campy/P3Steel-MGN-V19/P3Steel MGN BMG/Pegatina P3Steel/custom-industrial-write-on-signs-y4323289-65185-m8615-lg.jpg

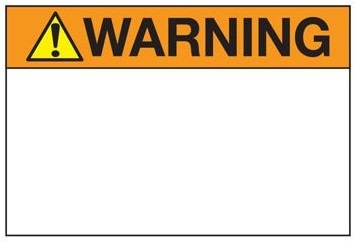
P3Steel MGN BMG/Pegatina P3Steel/custom-industrial-write-on-signs-y4323289-65185-m8615-lg.jpg
