campy/P3Steel-MGN-V19/P3Steel MGN BMG/Pegatina P3Steel/J6014.a24cb0112e51902b6b3ed4606a7cd727.png

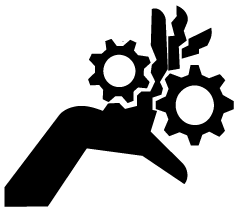
P3Steel MGN BMG/Pegatina P3Steel/J6014.a24cb0112e51902b6b3ed4606a7cd727.png
