campy/P3Steel-MGN-V19/P3Steel MGN BMG/Pegatina P3Steel/J6804.png

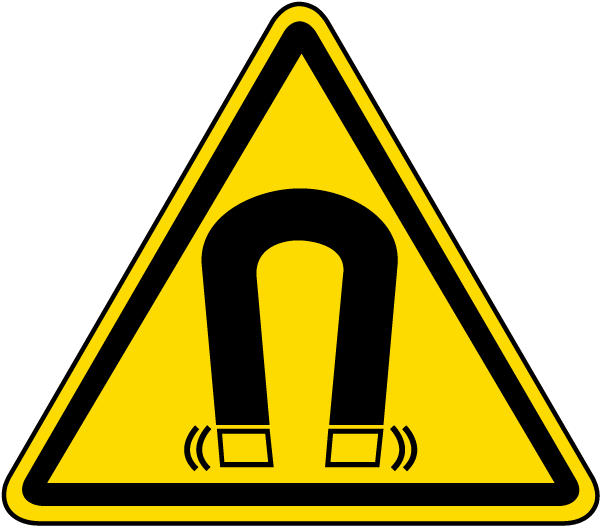
P3Steel MGN BMG/Pegatina P3Steel/J6804.png
