campy/P3Steel-MGN-V19/P3Steel MGN BMG/Pegatina P3Steel/p1725301.jpg

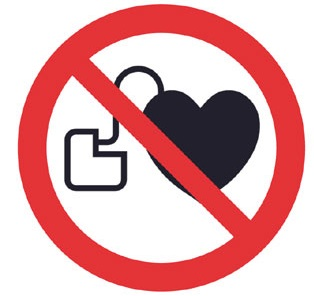
P3Steel MGN BMG/Pegatina P3Steel/p1725301.jpg
