campy/P3Steel-MGN-V19/P3Steel MGN BMG/Pegatina P3Steel/s-l1000.jpg

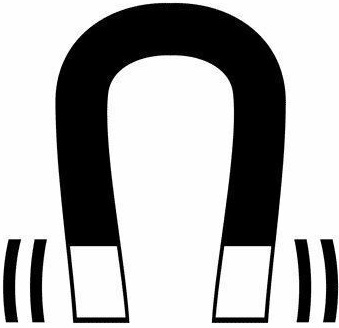
P3Steel MGN BMG/Pegatina P3Steel/s-l1000.jpg
