campy/P3Steel-MGN-V19/P3Steel MGN BMG/Piezas impresas/Soportes electronicas/Placas/MKS Gen L/Gen L.jpg

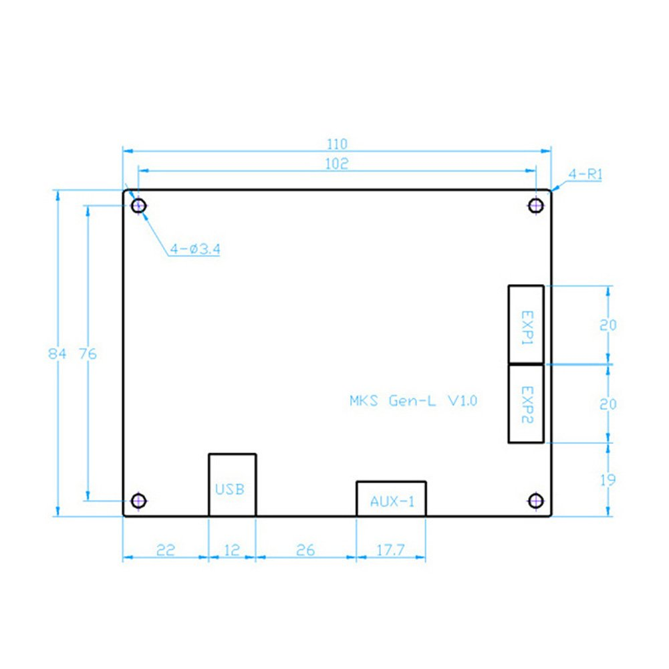
P3Steel MGN BMG/Piezas impresas/Soportes electronicas/Placas/MKS Gen L/Gen L.jpg
