campy/P3Steel-MGN-V19/P3Steel MGN BMG/Source/F-Sensor/Bildschirmfoto 2016-11-22 um 21.45.32.JPG

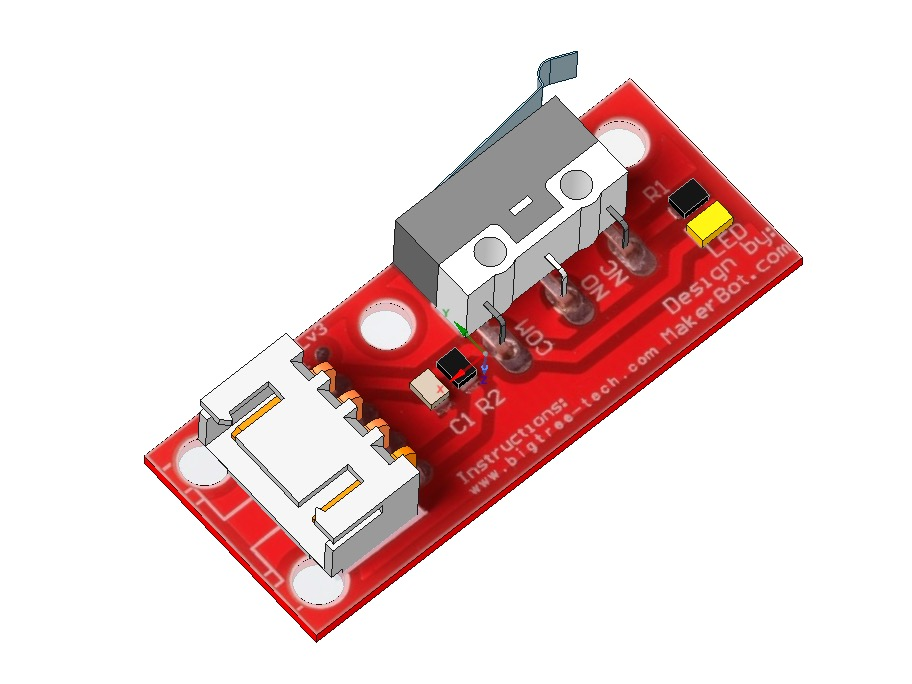
P3Steel MGN BMG/Source/F-Sensor/Bildschirmfoto 2016-11-22 um 21.45.32.JPG
