campy/P3Steel-MGN-V19/P3Steel MGN BMG/Source/Radial Cooling Fan 50mm DC12V/1.JPG

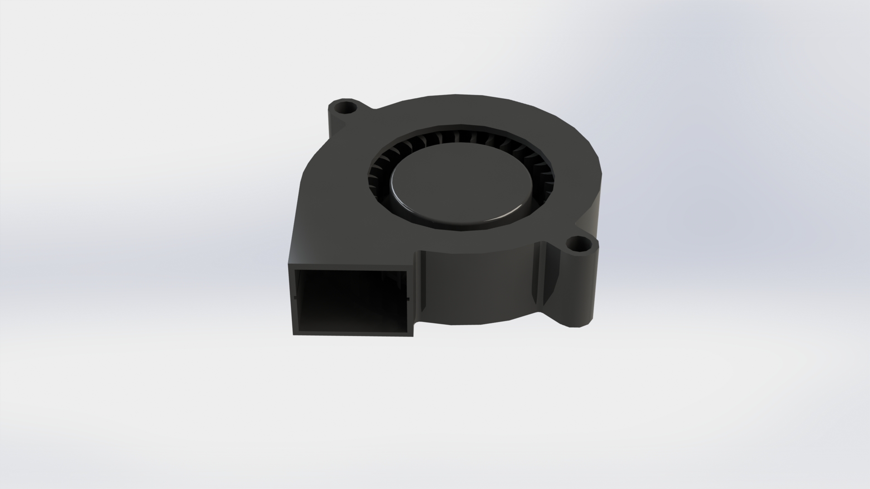
P3Steel MGN BMG/Source/Radial Cooling Fan 50mm DC12V/1.JPG
