campy/P3Steel-MGN-V19/P3Steel MGN BMG/Source/Radial Cooling Fan 50mm DC12V/5015 fan.PNG

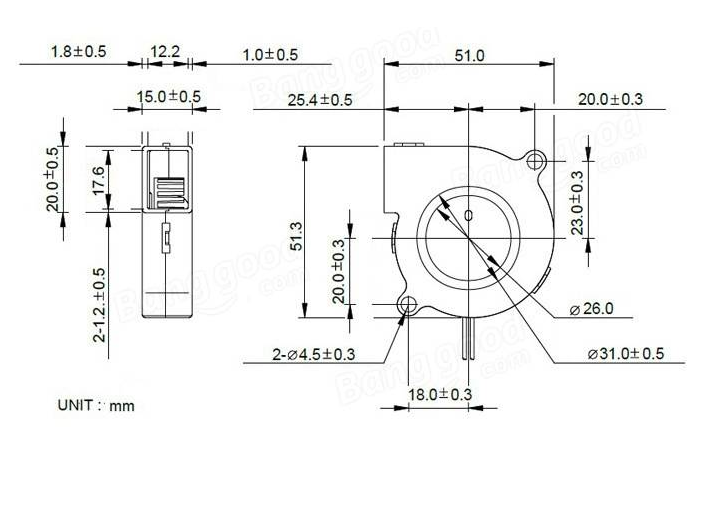
P3Steel MGN BMG/Source/Radial Cooling Fan 50mm DC12V/5015 fan.PNG
