campy/P3Steel-MGN-V19/P3Steel MGN BMG/Source/Radial Cooling Fan 50mm DC12V/Double-50-x-50-x-15mm-12V-DC-50mm-Blow-Radial-Cooling-Fan-for-Electronic-3D.jpg

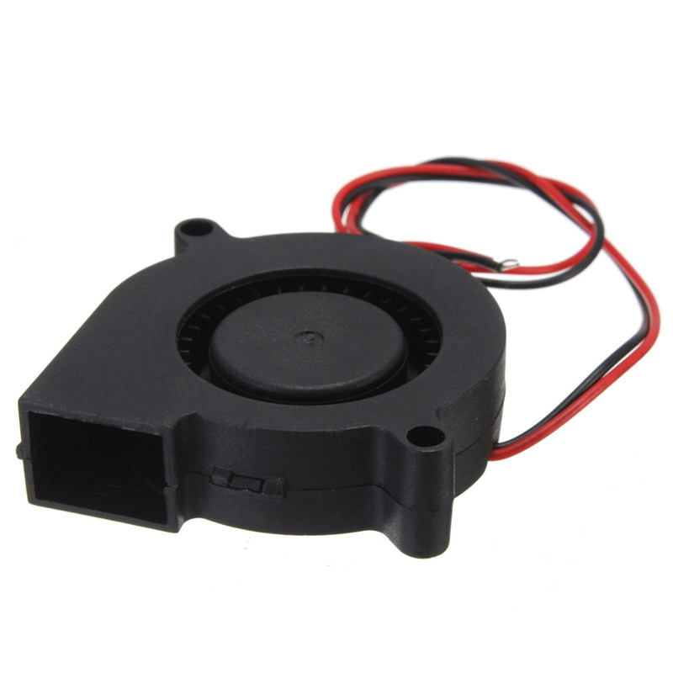
P3Steel MGN BMG/Source/Radial Cooling Fan 50mm DC12V/Double-50-x-50-x-15mm-12V-DC-50mm-Blow-Radial-Cooling-Fan-for-Electronic-3D.jpg
