campy/P3Steel-MGN-V19/P3Steel MGN BMG/Source/Titan Aero/Titan Aero P3steel/Blower titan/images/0aa3240f0cde22aaafeb0d4d7ab34d4f_preview_featured.jpg

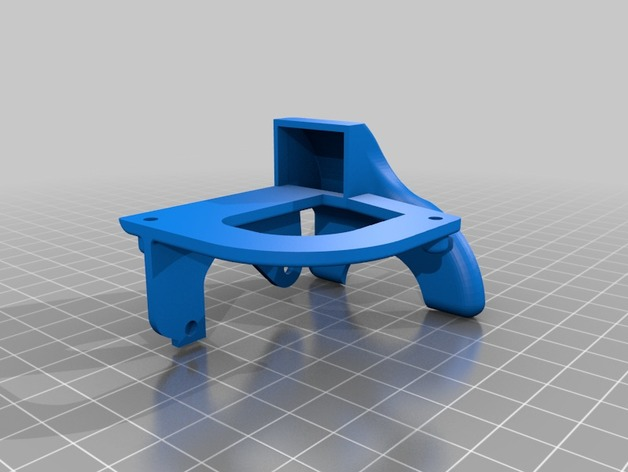
P3Steel MGN BMG/Source/Titan Aero/Titan Aero P3steel/Blower titan/images/0aa3240f0cde22aaafeb0d4d7ab34d4f_preview_featured.jpg
