campy/P3Steel-MGN-V19/P3Steel MGN BMG/Source/Titan Aero/Titan Aero P3steel/Blower titan/images/5dc998a0549c79088eb536fb6c97d659_preview_featured.jpg

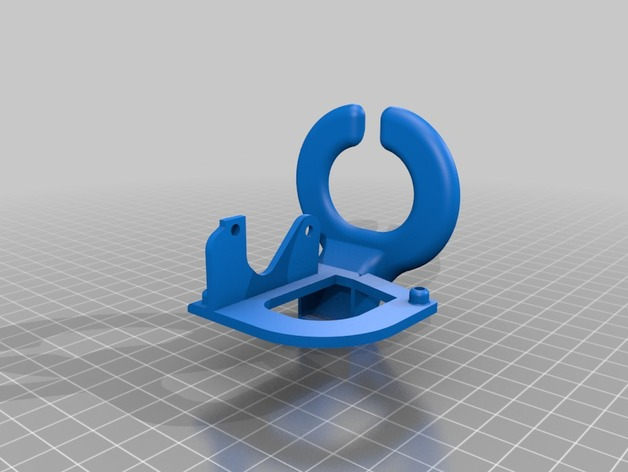
P3Steel MGN BMG/Source/Titan Aero/Titan Aero P3steel/Blower titan/images/5dc998a0549c79088eb536fb6c97d659_preview_featured.jpg
