campy/P3Steel-MGN-V19/P3Steel MGN BMG/Source/Titan Aero/Titan Aero P3steel/Blower titan/images/36a4d80571aeefbeef10a64a5f065d78_preview_featured.jpg

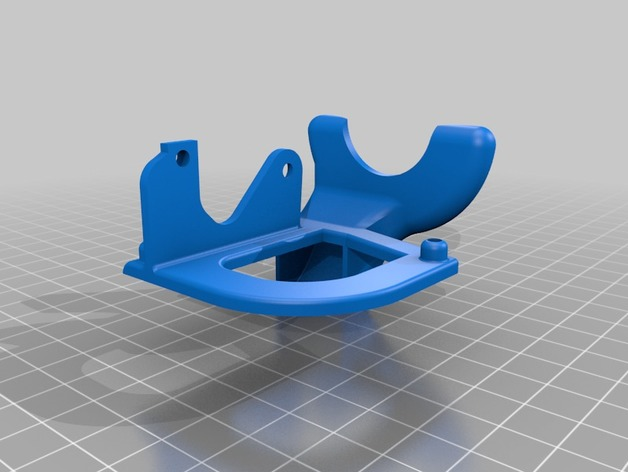
P3Steel MGN BMG/Source/Titan Aero/Titan Aero P3steel/Blower titan/images/36a4d80571aeefbeef10a64a5f065d78_preview_featured.jpg
