campy/P3Steel-MGN-V19/P3Steel MGN BMG/Source/Titan Aero/Titan Aero P3steel/Blower titan/images/036bd3c3c1cbe7b02644d6485af83f34_preview_featured.jpg

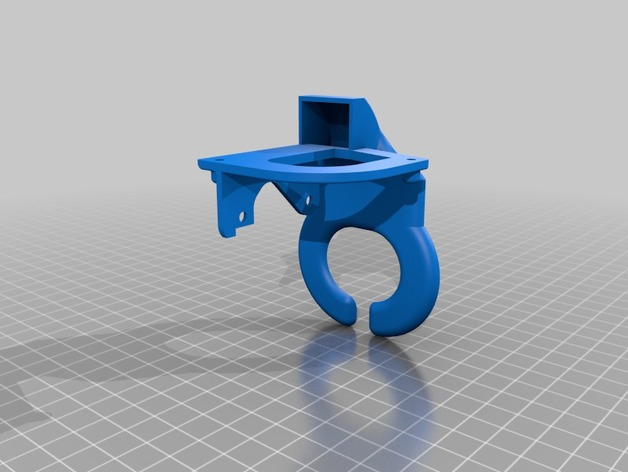
P3Steel MGN BMG/Source/Titan Aero/Titan Aero P3steel/Blower titan/images/036bd3c3c1cbe7b02644d6485af83f34_preview_featured.jpg
