campy/P3Steel-MGN-V19/P3Steel MGN BMG/Source/Titan Aero/Titan Aero P3steel/Blower titan/images/709aa3053908a7bdff81a3a324b6f3b1_preview_featured.jpg

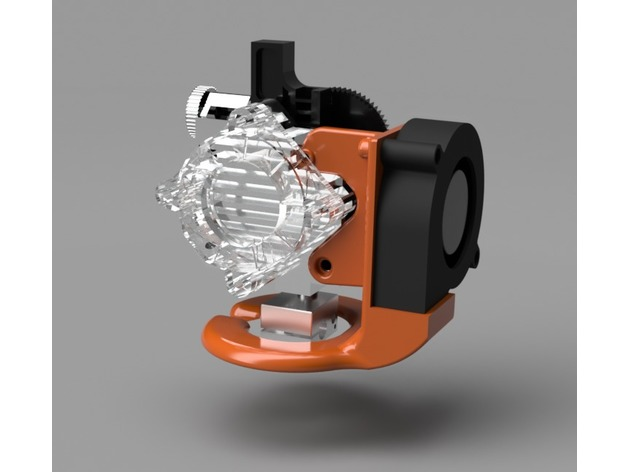
P3Steel MGN BMG/Source/Titan Aero/Titan Aero P3steel/Blower titan/images/709aa3053908a7bdff81a3a324b6f3b1_preview_featured.jpg
