campy/P3Steel-MGN-V19/P3Steel MGN BMG/Source/Titan Aero/Titan Aero P3steel/Blower titan/images/1118b5d8f00bb2cfa117ddb364b9ccff_preview_featured.jpg

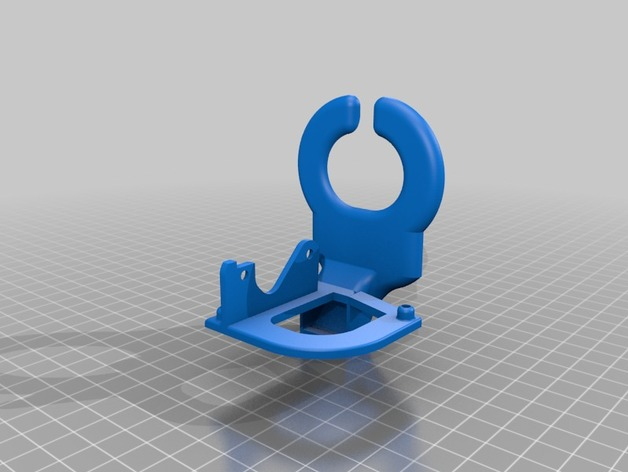
P3Steel MGN BMG/Source/Titan Aero/Titan Aero P3steel/Blower titan/images/1118b5d8f00bb2cfa117ddb364b9ccff_preview_featured.jpg
