campy/P3Steel-MGN-V19/P3Steel MGN BMG/Source/Titan Aero/Titan Aero P3steel/Blower titan/images/51332b5f8a75edf978d1d0842197646b_preview_featured.jpg

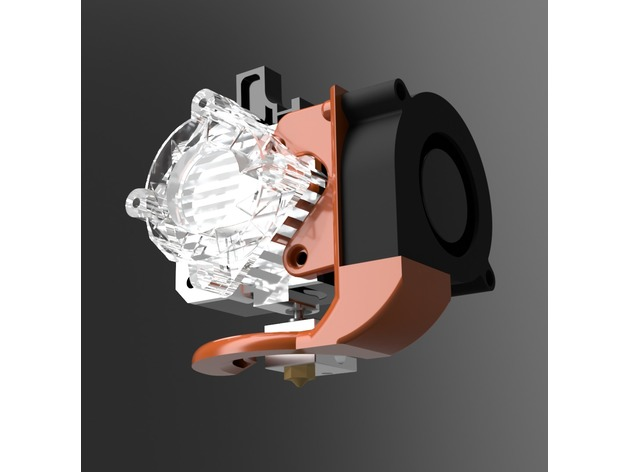
P3Steel MGN BMG/Source/Titan Aero/Titan Aero P3steel/Blower titan/images/51332b5f8a75edf978d1d0842197646b_preview_featured.jpg
