campy/P3Steel-MGN-V19/P3Steel MGN BMG/Source/Titan Aero/Titan Aero P3steel/Blower titan/images/825169e0491ec67ebed7de5d310a97ef_preview_featured.jpg

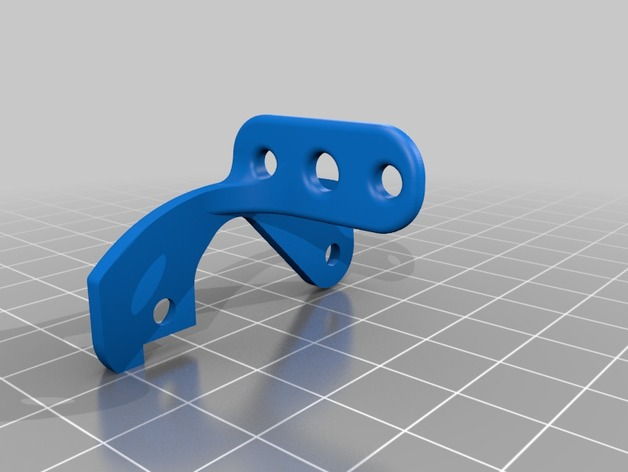
P3Steel MGN BMG/Source/Titan Aero/Titan Aero P3steel/Blower titan/images/825169e0491ec67ebed7de5d310a97ef_preview_featured.jpg
