campy/P3Steel-MGN-V19/P3Steel MGN BMG/Source/Titan Aero/Titan Aero P3steel/Blower titan/images/dfa683ba2eb11ce575a9aa6dc8c6160b_preview_featured.jpg

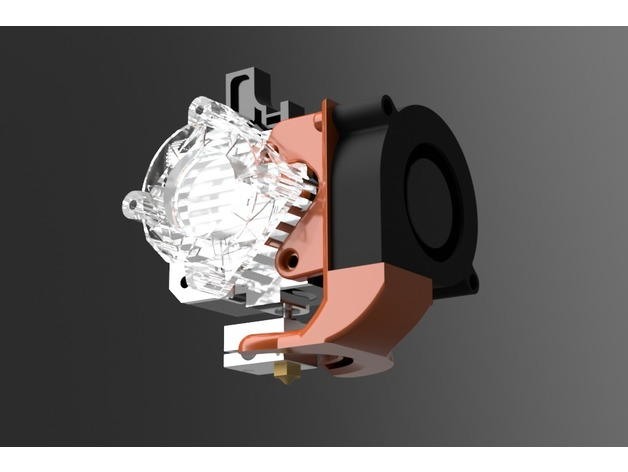
P3Steel MGN BMG/Source/Titan Aero/Titan Aero P3steel/Blower titan/images/dfa683ba2eb11ce575a9aa6dc8c6160b_preview_featured.jpg
