campy/P3Steel-MGN-V19/P3Steel MGN BMG/Source/Tuerca Anti-Back/TR08.bmp

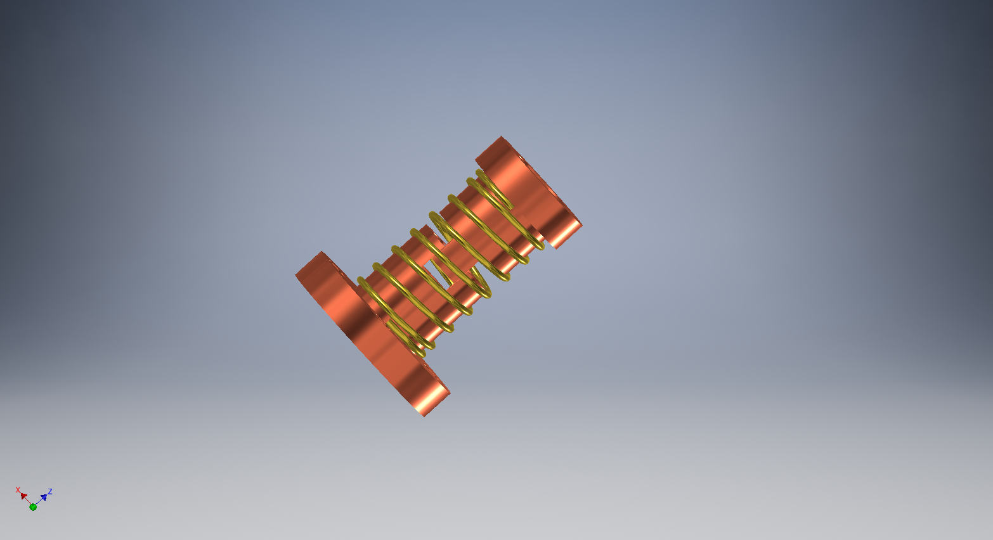
P3Steel MGN BMG/Source/Tuerca Anti-Back/TR08.bmp
