campy/P3Steel-MGN-V19/P3Steel MGN Titan/Capturas/16.png

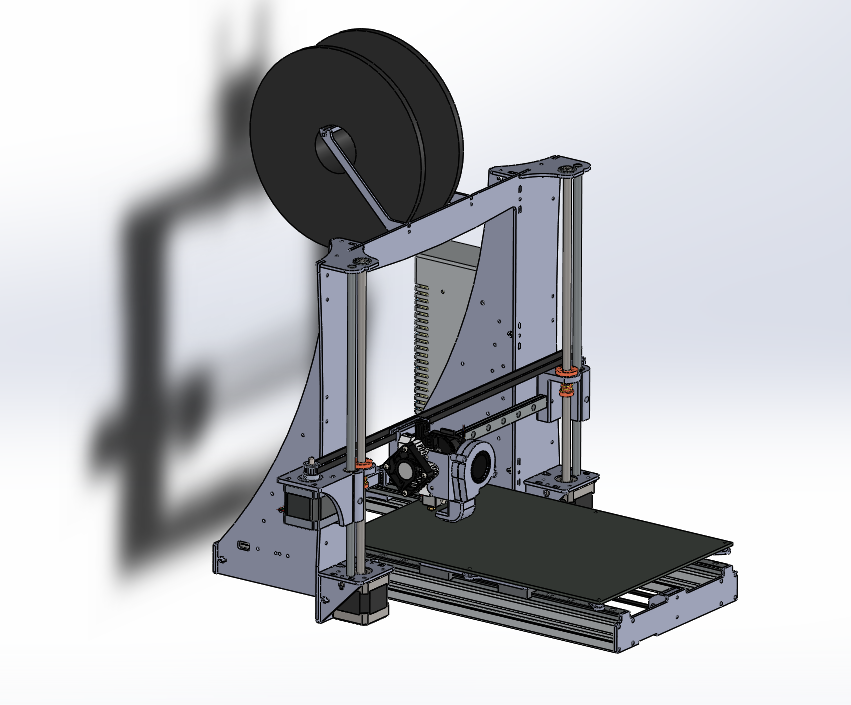
P3Steel MGN Titan/Capturas/16.png
