campy/P3Steel-MGN-V19/P3Steel MGN Titan/Capturas/Proto1.jpg

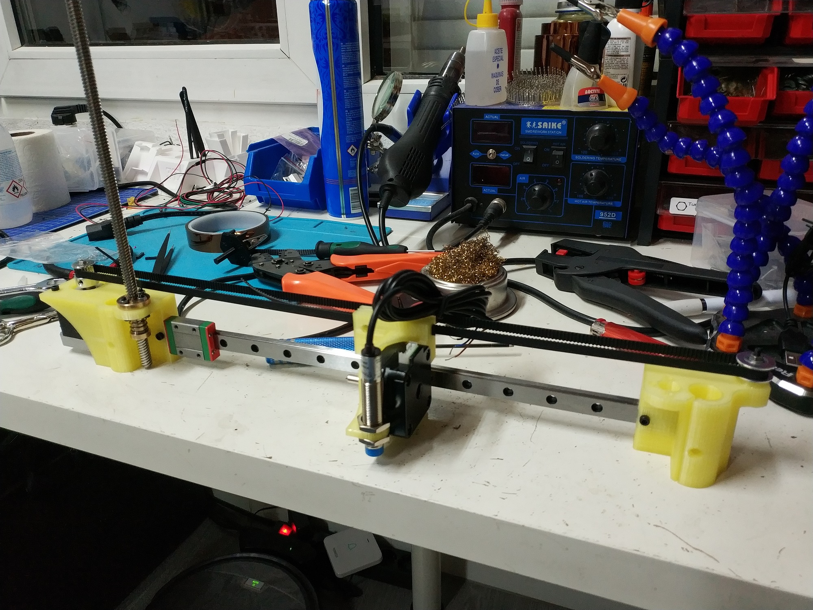
P3Steel MGN Titan/Capturas/Proto1.jpg
