campy/P3Steel-MGN-V19/P3Steel MGN Titan/Source/Mot Y/Mot Y.SLDASM

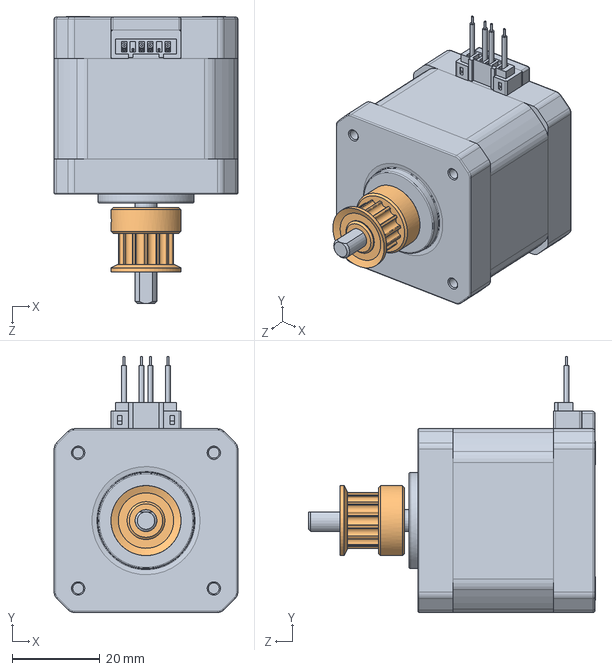
[picture p54: CAD file, 2019-09-07]
P3Steel MGN Titan/Source/Mot Y/Mot Y.SLDASM
42.0 x 58.5 x 65.7 mm
nema_17_motor
Polea GT2
