campy/P3Steel-MGN-V19/P3Steel MGN Titan/Source/Nema Y/Stepper motor/Nema Z2.SLDASM

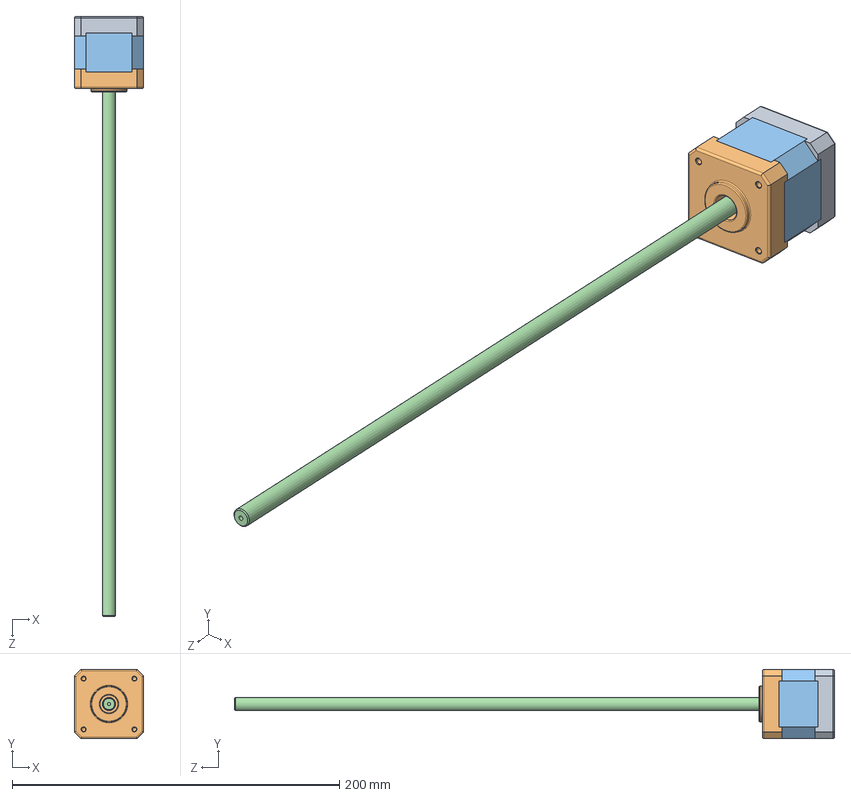
[picture p55: CAD file, 2019-09-07]
P3Steel MGN Titan/Source/Nema Y/Stepper motor/Nema Z2.SLDASM
42.3 x 42.3 x 366.5 mm
