campy/P3Steel-MGN-V19/P3Steel MGN BMG/Piezas impresas/Cadenetas/Cadeneta 15/Otros/Ensamblaje Eslabon 15.SLDASM

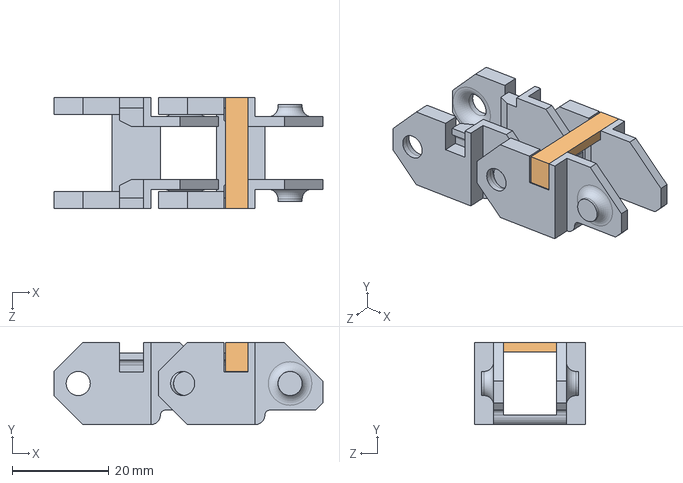
[picture p56: CAD file, 2019-06-21]
P3Steel MGN BMG/Piezas impresas/Cadenetas/Cadeneta 15/Otros/Ensamblaje Eslabon 15.SLDASM
55.6 x 17.0 x 23.0 mm
Eslabon 15 x 2
Cierre 15
