campy/P3Steel-MGN-V19/P3Steel MGN BMG/Piezas impresas/Cadenetas/Cadeneta 5/EnsamblajeBandejaY.SLDASM

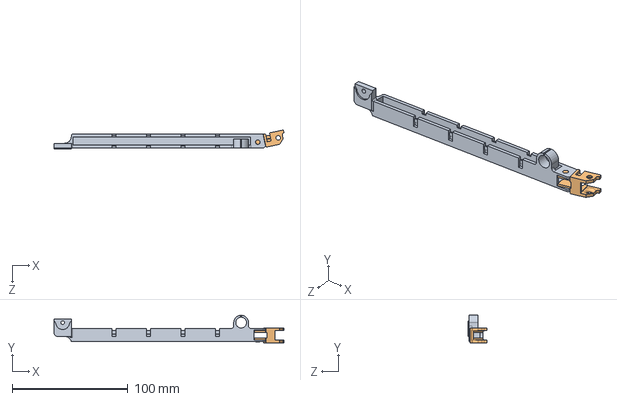
[picture p57: CAD file, 2019-09-13]
P3Steel MGN BMG/Piezas impresas/Cadenetas/Cadeneta 5/EnsamblajeBandejaY.SLDASM
199.1 x 23.9 x 16.5 mm
Soporte Base V2
Eslabon 5 Bloqueado
