campy/P3Steel-MGN-V19/P3Steel MGN Titan/Piezas impresas/Cadenetas/Cadeneta 5/Otros Tipos Eslabones/Ensamblaje1.SLDASM

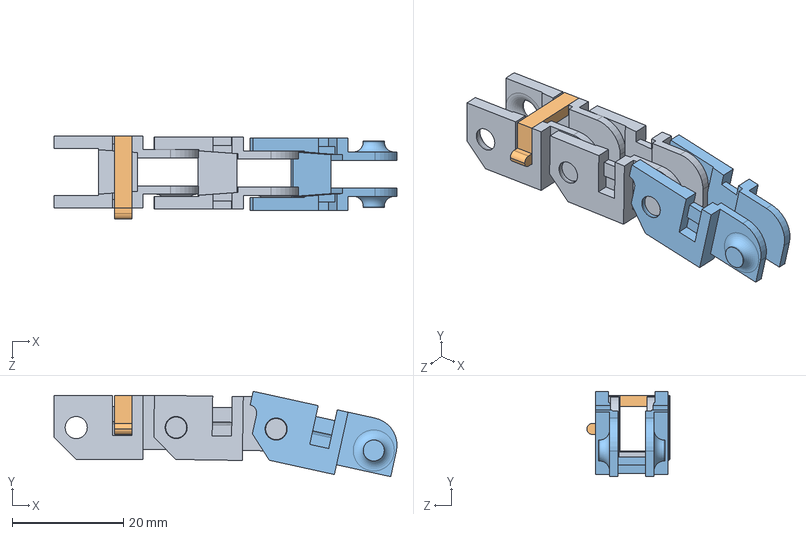
[picture p58: CAD file, 2019-06-21]
P3Steel MGN Titan/Piezas impresas/Cadenetas/Cadeneta 5/Otros Tipos Eslabones/Ensamblaje1.SLDASM
61.8 x 15.4 x 15.0 mm
Eslabon 5 x 2
Cierre 5
Eslabon 5 Bloqueado
