campy/P3Steel-MGN-V19/P3Steel MGN Titan/Piezas impresas/F-Sensor/Sensor filamento 2.0/Ensamblaje sensor filamento.SLDASM

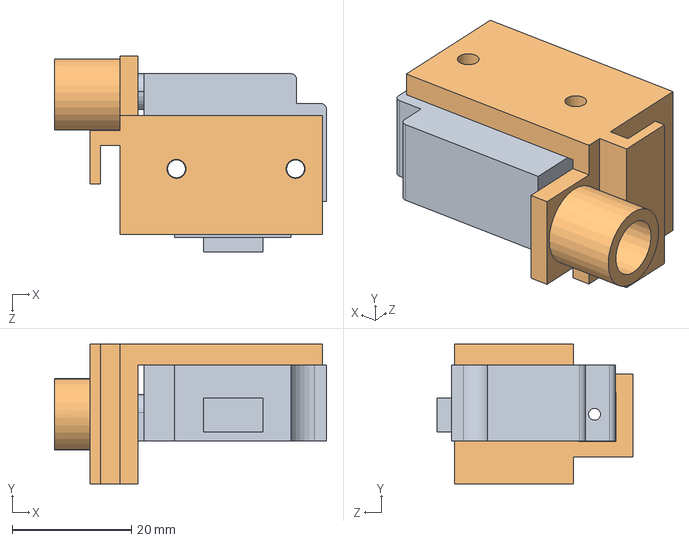
[picture p59: CAD file, 2019-09-07]
P3Steel MGN Titan/Piezas impresas/F-Sensor/Sensor filamento 2.0/Ensamblaje sensor filamento.SLDASM
45.7 x 23.5 x 33.0 mm
Sensor filamento
Soporte sensor filamento
