campy/P3Steel-MGN-V19/P3Steel MGN Titan/Source/Conector C14/switch.SLDASM

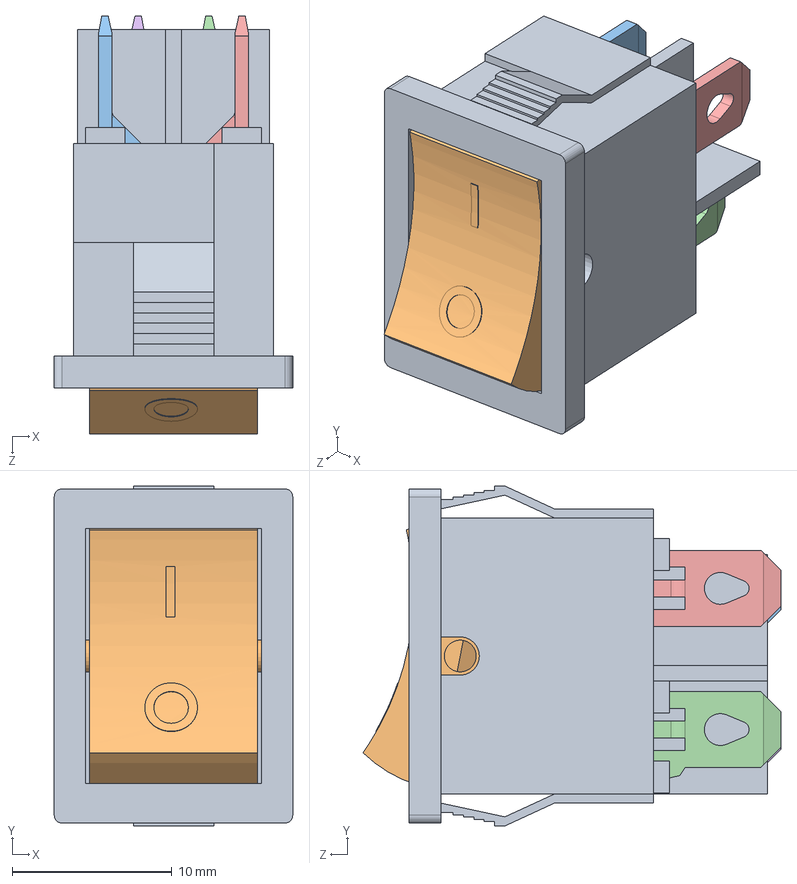
[picture p60: CAD file, 2019-09-07]
P3Steel MGN Titan/Source/Conector C14/switch.SLDASM
14.9 x 21.3 x 26.2 mm
switch_base
rocker
sm_tab_type1a
sm_tab_type1b
sm_tab_type2a
sm_tab_type2b
