campy/P3Steel-MGN-V19/P3Steel MGN Titan/Source/F688zz/F688ZZ_assembly.SLDASM

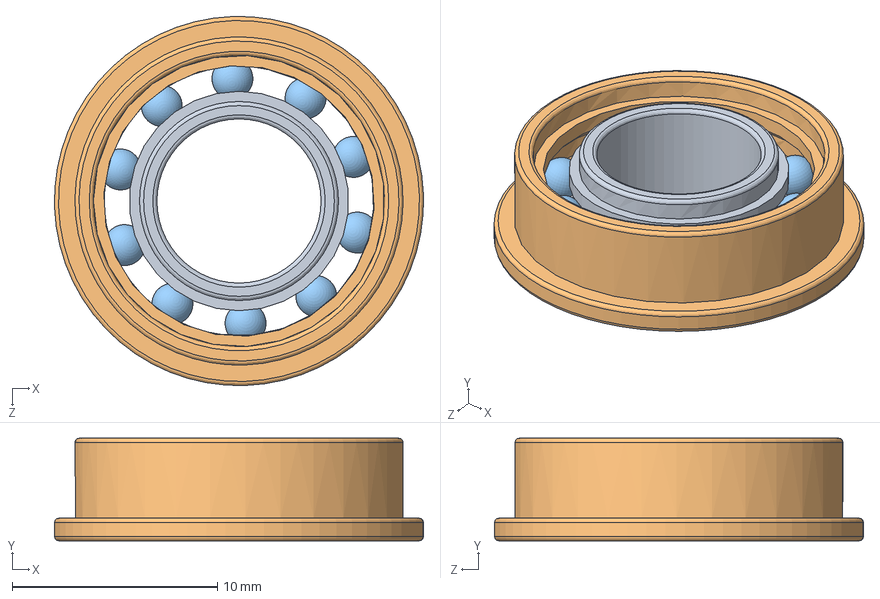
[picture p61: CAD file, 2019-06-21]
P3Steel MGN Titan/Source/F688zz/F688ZZ_assembly.SLDASM
18.0 x 5.00 x 18.0 mm
F688ZZ_shaft
F688ZZ_Housing
F688ZZ_Ball x 10
