campy/P3Steel-MGN-V19/P3Steel MGN BMG/Piezas impresas/F-Sensor/Sensor con endstop/Ensamblaje F-Sensor.SLDASM

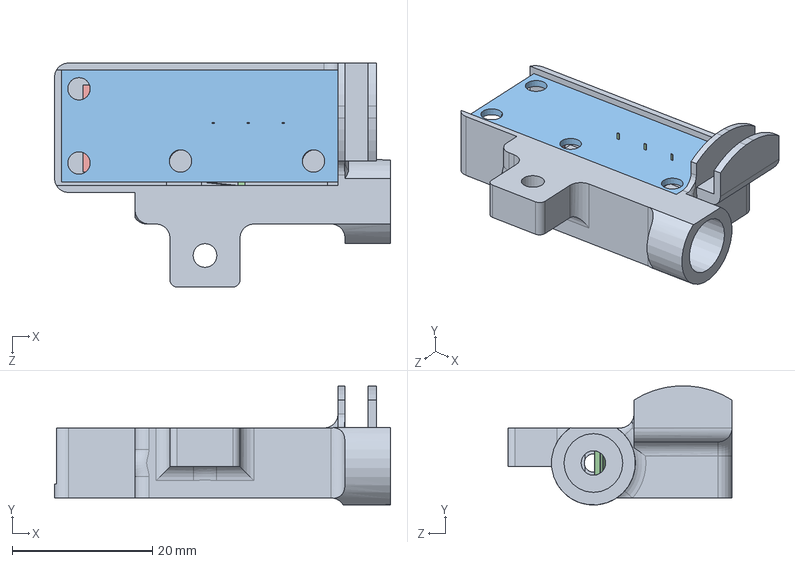
[picture p62: CAD file, 2019-06-21]
P3Steel MGN BMG/Piezas impresas/F-Sensor/Sensor con endstop/Ensamblaje F-Sensor.SLDASM
48.0 x 17.0 x 32.0 mm
Soporte F-Sensor
Konstruktion24
PCB^Endstop
Microswitch_1A_125vAC(seul)
JST 4Pin
