campy/P3Steel-MGN-V19/P3Steel MGN BMG/Source/BMG/E3dSimple/ED3V6 v3.sldasm

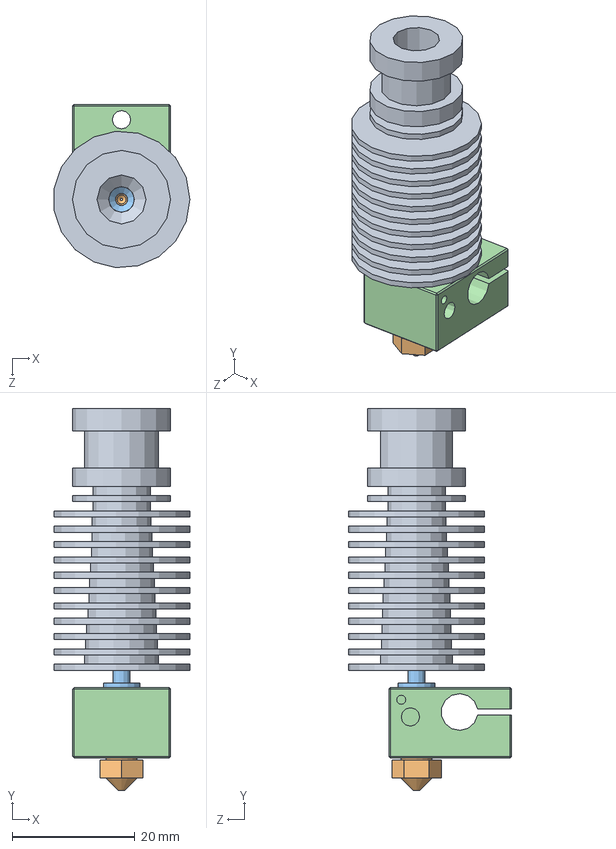
[picture p63: CAD file, 2019-09-13]
P3Steel MGN BMG/Source/BMG/E3dSimple/ED3V6 v3.sldasm
22.1 x 62.3 x 26.6 mm
HEATSINK
NOZZLE 0
HEATBRICK
HEATERBLOCK
