campy/P3Steel-MGN-V19/P3Steel MGN Titan/Source/F-Sensor/Endstop Led.SLDASM

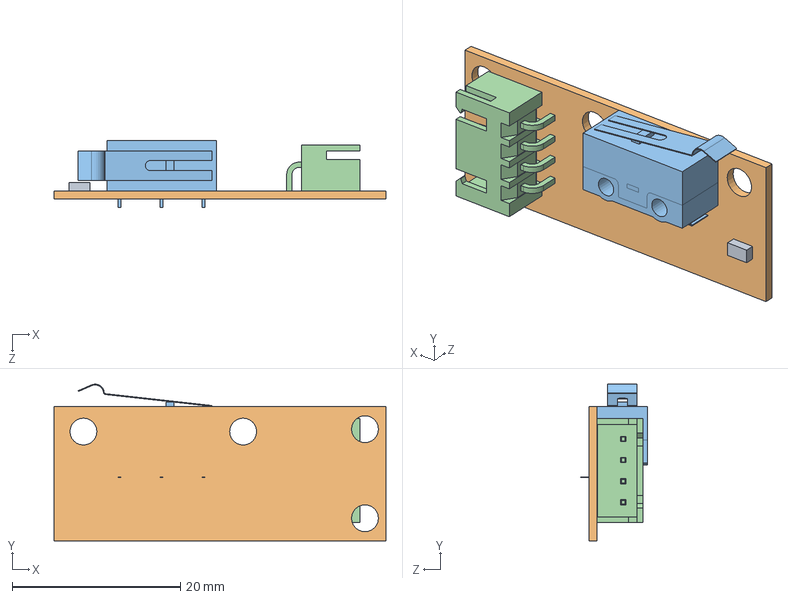
[picture p64: CAD file, 2019-06-21]
P3Steel MGN Titan/Source/F-Sensor/Endstop Led.SLDASM
39.5 x 18.6 x 8.00 mm
Konstruktion24
PCB^Endstop
Microswitch_1A_125vAC(seul)
JST 4Pin
