campy/P3Steel-MGN-V19/P3Steel MGN BMG/Ensamblaje-Xmotor.SLDASM

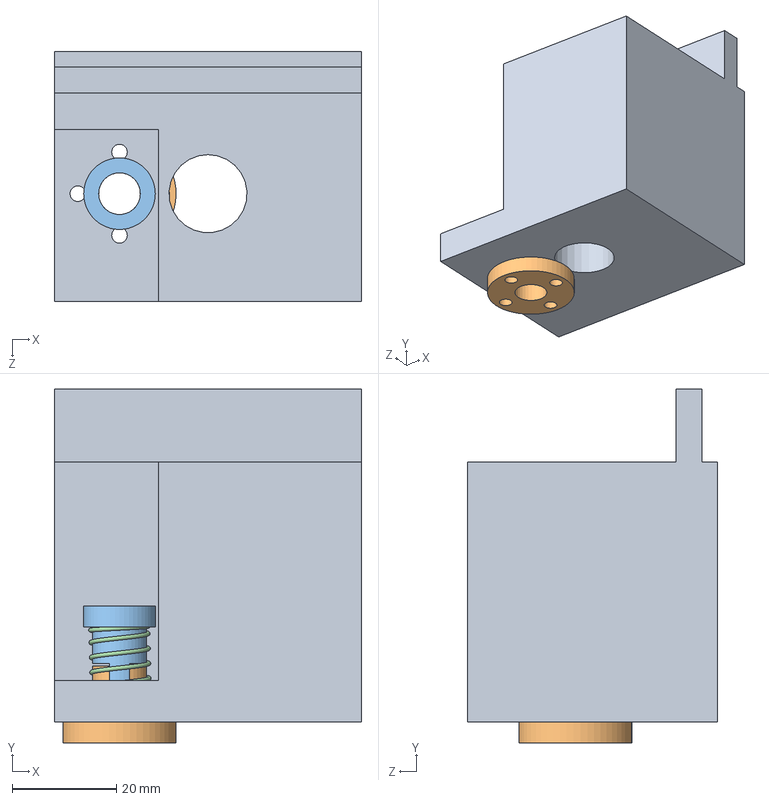
[picture p65: CAD file, 2019-09-13]
P3Steel MGN BMG/Ensamblaje-Xmotor.SLDASM
59.0 x 68.0 x 48.0 mm
X motor
nakretka tr08
napinacz nakretki tr8
sprezyna nakretka tr 8
