campy/P3Steel-MGN-V19/P3Steel MGN BMG/Piezas impresas/Cadenetas/Cadeneta 15/Ensamblaje Eslabon 15.SLDASM

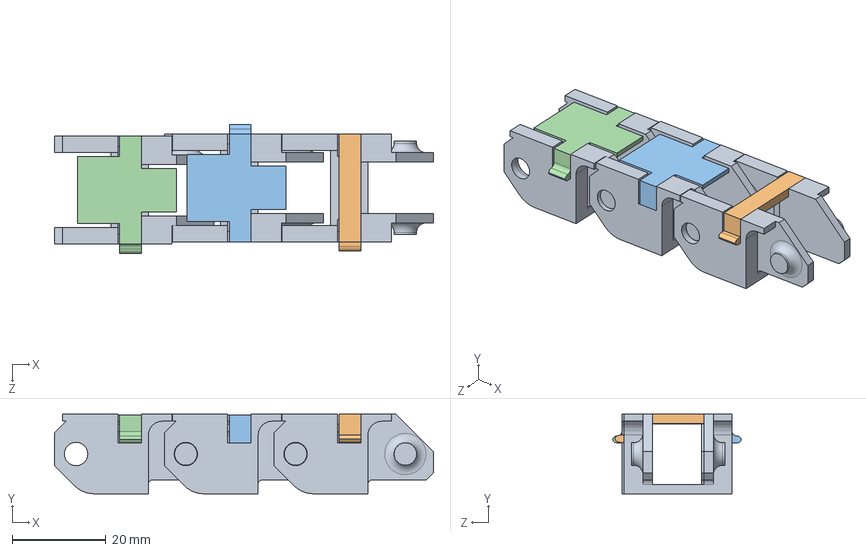
[picture p66: CAD file, 2019-06-21]
P3Steel MGN BMG/Piezas impresas/Cadenetas/Cadeneta 15/Ensamblaje Eslabon 15.SLDASM
80.8 x 17.0 x 27.4 mm
Eslabon 15 x 3
Cierre 15
Cierre 15 Tapa R
Cierre 15 Tapa L
