campy/P3Steel-MGN-V19/P3Steel MGN BMG/Source/MGN12/MGN12-450.SLDASM

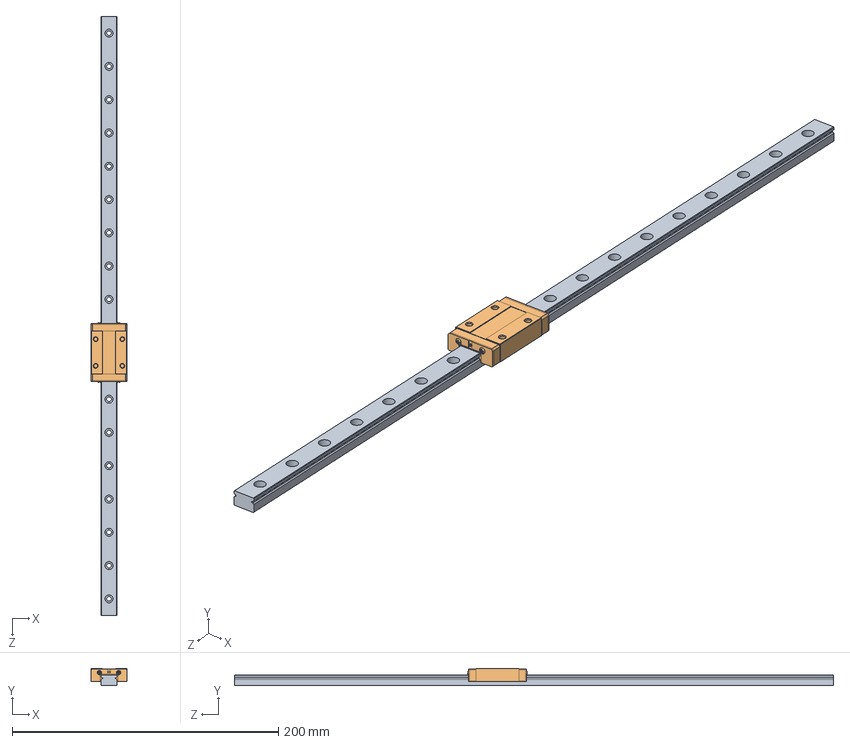
[picture p67: CAD file, 2019-06-21]
P3Steel MGN BMG/Source/MGN12/MGN12-450.SLDASM
27.0 x 13.0 x 450.0 mm
MGN12_450
MGN12-H
