campy/P3Steel-MGN-V19/P3Steel MGN BMG/Source/BMG/E3dSimple/fan.SLDASM

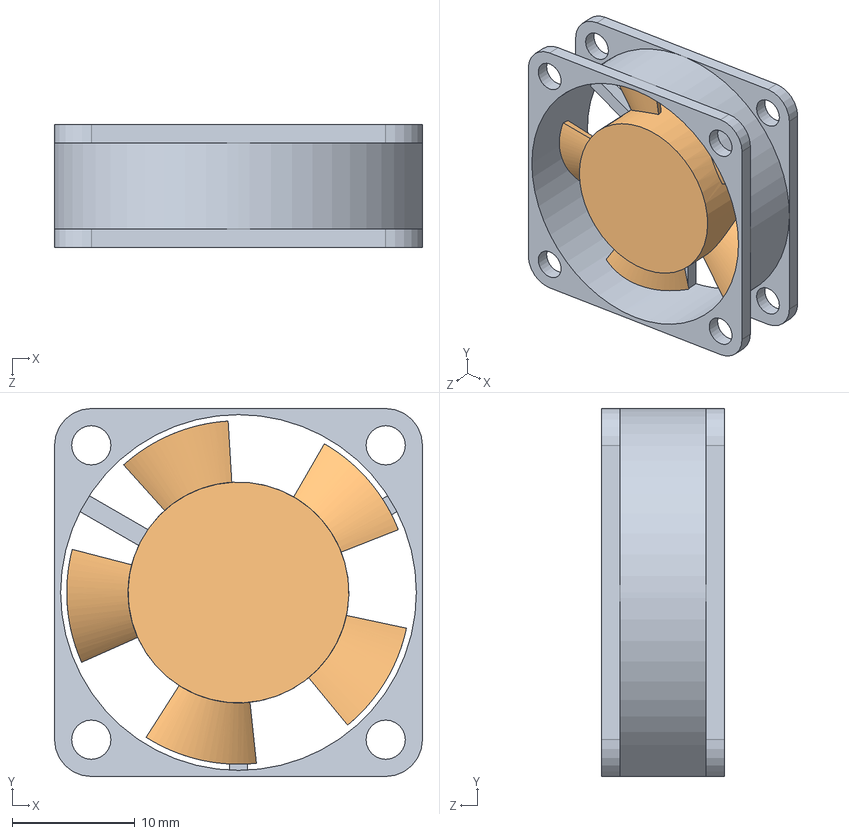
[picture p69: CAD file, 2019-09-13]
P3Steel MGN BMG/Source/BMG/E3dSimple/fan.SLDASM
30.0 x 30.0 x 10.0 mm
fan sub1
fan sub2
