campy/P3Steel-MGN-V19/P3Steel MGN BMG/Source/Nema Y/Stepper motor/Stepper motor Assy.SLDASM

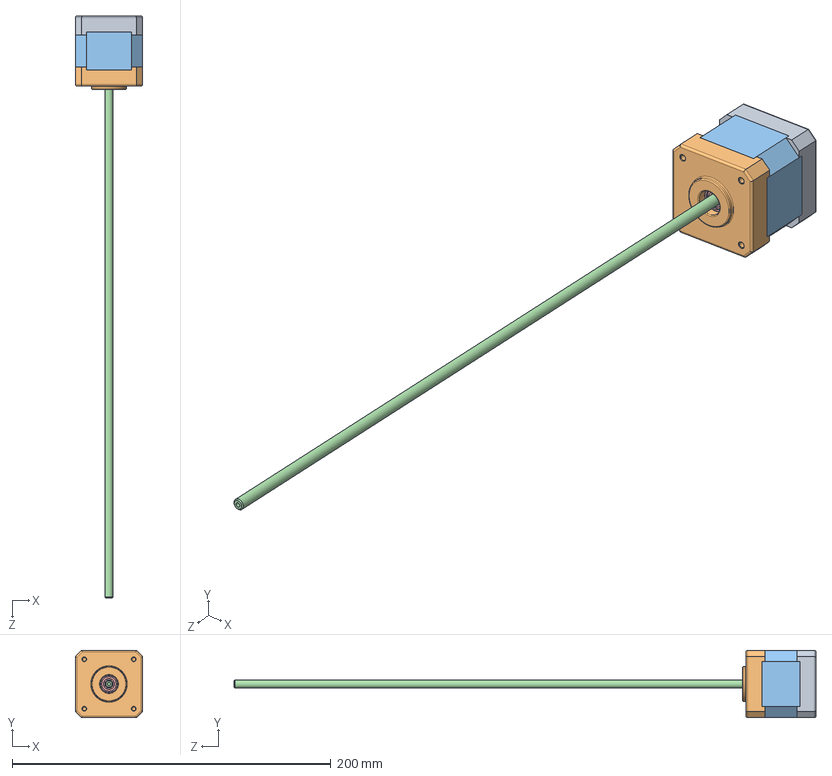
[picture p70: CAD file, 2019-06-21]
P3Steel MGN BMG/Source/Nema Y/Stepper motor/Stepper motor Assy.SLDASM
42.3 x 42.3 x 365.0 mm
radial ball bearing_68_iso x 2
pan head cross recess screw_iso x 4
