campy/P3Steel-MGN-V19/P3Steel MGN BMG/Source/BMG/E3dSimple/fanduct.SLDASM

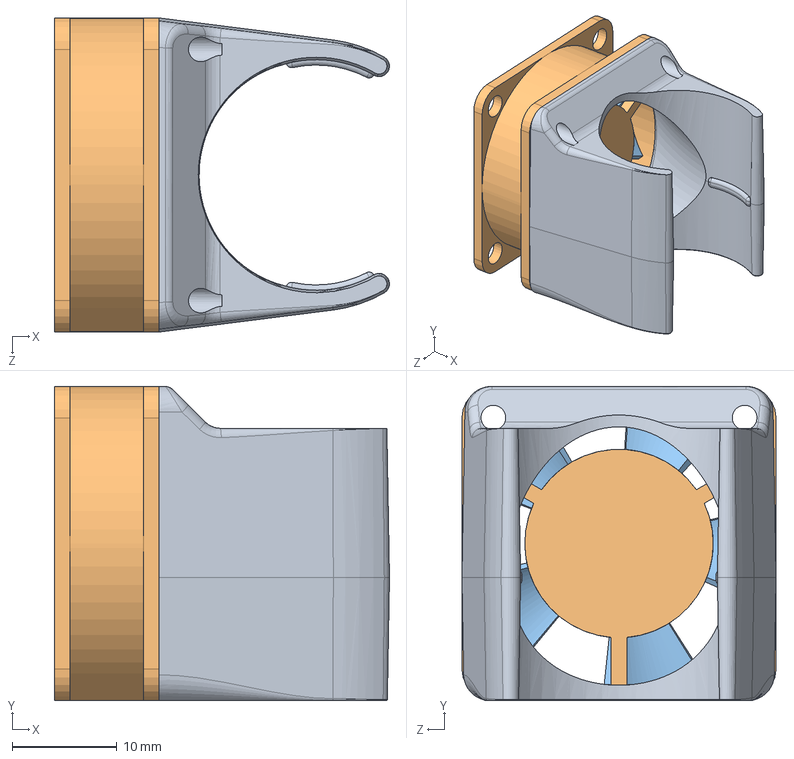
[picture p71: CAD file, 2019-09-13]
P3Steel MGN BMG/Source/BMG/E3dSimple/fanduct.SLDASM
32.0 x 30.0 x 30.0 mm
fan duct
fan sub1
fan sub2
