campy/P3Steel-MGN-V19/P3Steel MGN Titan/Piezas impresas/Cadenetas/Cadeneta 5/Ensamblaje Eslabones.SLDASM

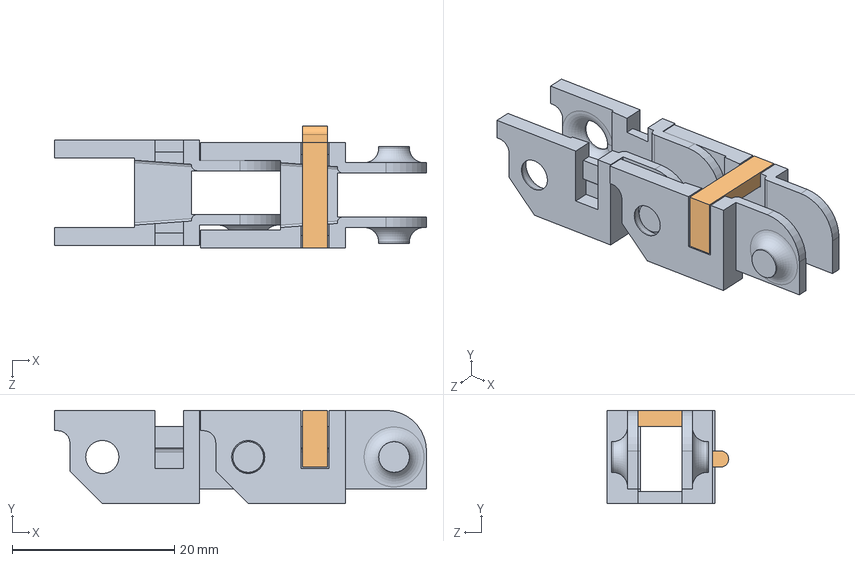
[picture p72: CAD file, 2019-06-21]
P3Steel MGN Titan/Piezas impresas/Cadenetas/Cadeneta 5/Ensamblaje Eslabones.SLDASM
45.9 x 11.5 x 15.0 mm
Eslabon 5 Bloqueado x 2
Cierre 5
