campy/P3Steel-MGN-V19/P3Steel MGN BMG/Source/MGN12/Assem1.SLDASM

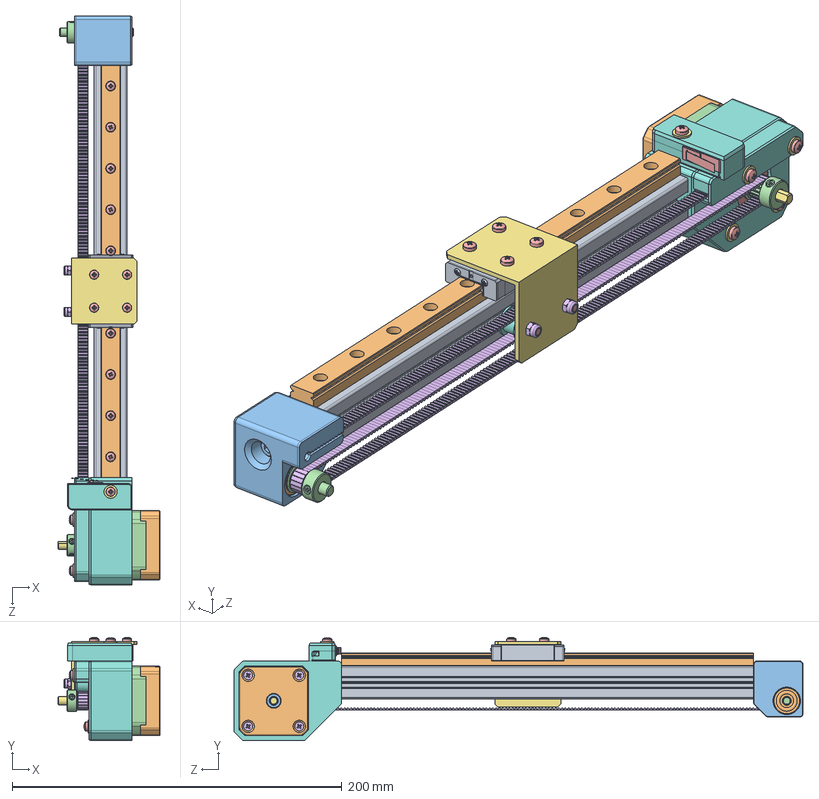
[picture p74: CAD file, 2019-06-21]
P3Steel MGN BMG/Source/MGN12/Assem1.SLDASM
62.0 x 62.7 x 345.2 mm
rsi_2020_274
nema17_bottom_40mm
radial ball bearing_68_din x 2
nema17_middle_40mm
nema17_top_40mm
countersunk flat head cross recess screw_din x 4
nema17_shaft_40mm
nema17_mount_1
MGN12-H
MGN12_250
idle_pul_mount_1
GT2_16T_13x14 x 2
SS-5GL_microswitch
belt_250
alum_40x40x2
idle_pulley_16 x 2
mgn12_fix x 5
instrument ball bearing_68_am x 2
socket head cap screw_am x 2
continous stud_am
pan head cross recess screw_din x 21
prevailing torque nut style 1 insert_din x 2
plain washer 6902 type abc_din x 5
hex nut style 1 gradeab_din x 10
