campy/P3Steel-MGN-V19/P3Steel MGN Titan/Piezas impresas/Soportes electronicas/Placas/Duet Wifi/Duet WIfi Rev 4.SLDASM

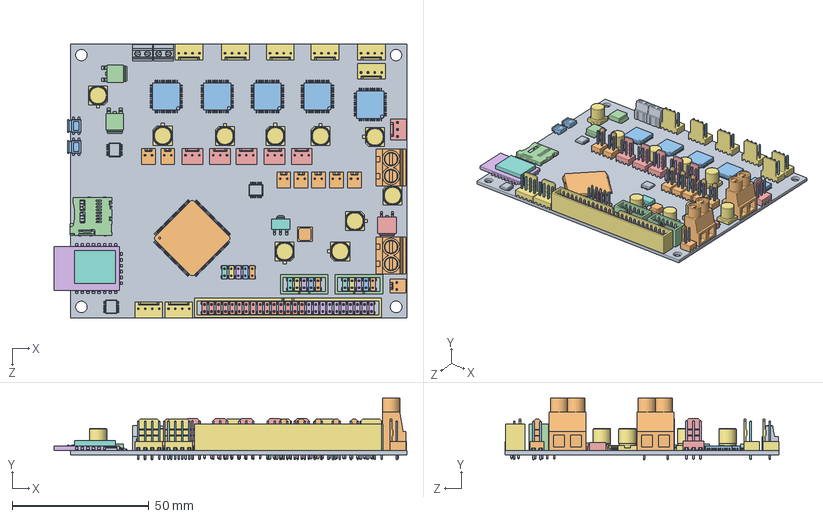
[picture p75: CAD file, 2019-09-07]
P3Steel MGN Titan/Piezas impresas/Soportes electronicas/Placas/Duet Wifi/Duet WIfi Rev 4.SLDASM
129.0 x 22.5 x 100.0 mm
Main PCB v56
BASE9710016_1 x 8
PINO9710016_1 x 16
microSD1 v4
BASE9710016_2 x 6
PINO9710016_2 x 18
BASE9710016 x 8
PINO9710016 x 32
2 pole terminal block v7 x 2
2 pole terminal block large v7 x 2
MOSFET v9 x 2
Power reg v5
Power reg R2 v4
choke v6
button switch v9 x 2
Pin Header 2x15 TH Pitch 2.54mm v2
Pin Header 2x10 TH Pitch 2.54mm v2
wifi chip v3
