campy/P3Steel-MGN-V19/P3Steel MGN BMG/Escuadra Central.SLDPRT

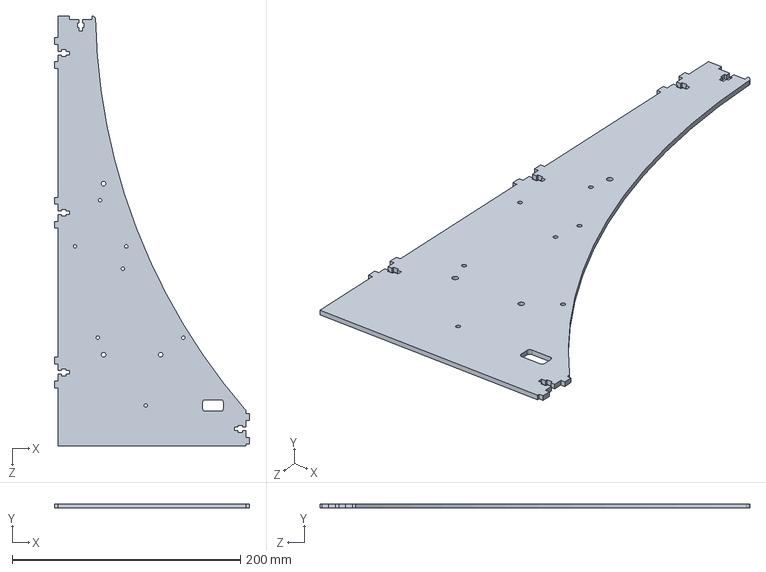
[picture p77: CAD file, 2019-09-13]
P3Steel MGN BMG/Escuadra Central.SLDPRT
171.0 x 3.20 x 377.0 mm
