campy/P3Steel-MGN-V19/P3Steel MGN BMG/Extrusor/X-CarriageV2 BMG.SLDPRT

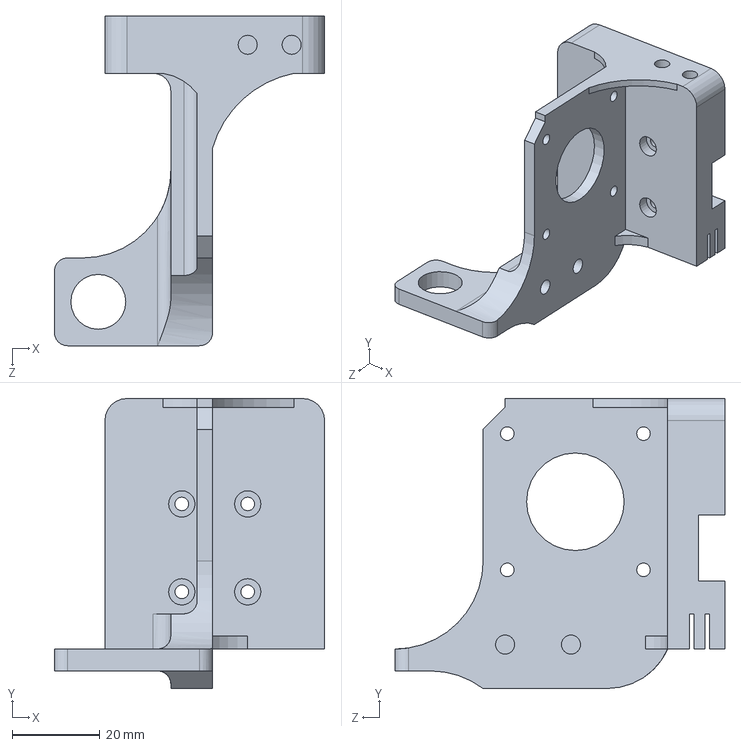
[picture p78: CAD file, 2019-09-13]
P3Steel MGN BMG/Extrusor/X-CarriageV2 BMG.SLDPRT
61.5 x 66.0 x 75.0 mm
