campy/P3Steel-MGN-V19/P3Steel MGN BMG/Piezas impresas/Cadenetas/Cadeneta 15/Otros/Cierre 15.SLDPRT

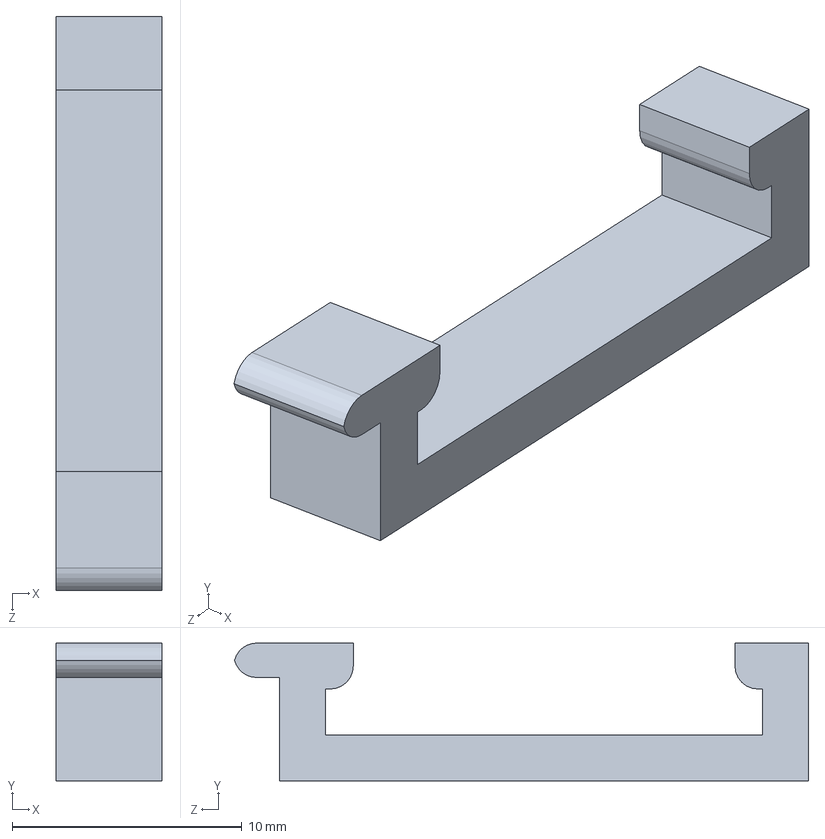
[picture p79: CAD file, 2019-06-21]
P3Steel MGN BMG/Piezas impresas/Cadenetas/Cadeneta 15/Otros/Cierre 15.SLDPRT
4.60 x 6.00 x 25.0 mm
