campy/P3Steel-MGN-V19/P3Steel MGN BMG/Piezas impresas/Cadenetas/Cadeneta 15/Soporte XMotor.SLDPRT

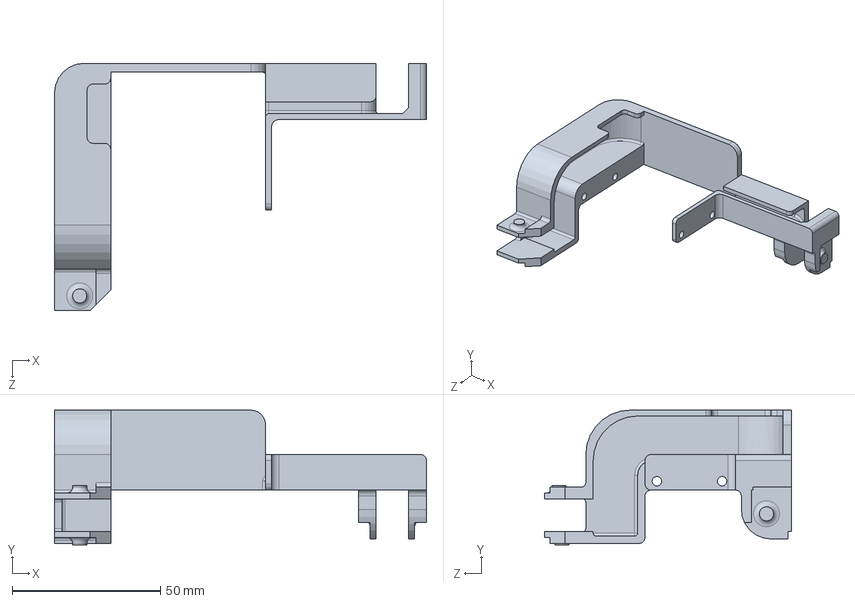
[picture p80: CAD file, 2019-09-13]
P3Steel MGN BMG/Piezas impresas/Cadenetas/Cadeneta 15/Soporte XMotor.SLDPRT
125.5 x 45.5 x 83.5 mm
