campy/P3Steel-MGN-V19/P3Steel MGN BMG/Piezas impresas/Cadenetas/Cadeneta 5/Otros Tipos Eslabones/Eslabon 5.SLDPRT

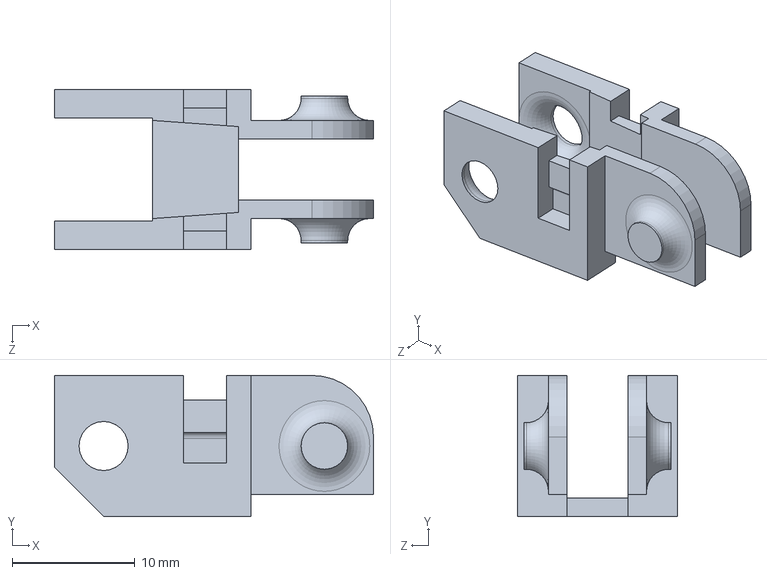
[picture p81: CAD file, 2019-06-21]
P3Steel MGN BMG/Piezas impresas/Cadenetas/Cadeneta 5/Otros Tipos Eslabones/Eslabon 5.SLDPRT
26.0 x 11.5 x 13.0 mm
