campy/P3Steel-MGN-V19/P3Steel MGN BMG/Piezas impresas/Cadenetas/Cadeneta 5/Soporte electronica.SLDPRT

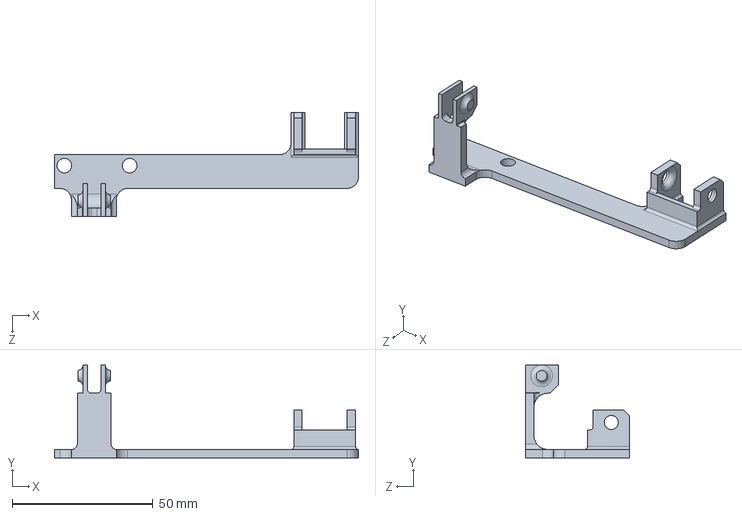
[picture p82: CAD file, 2019-09-13]
P3Steel MGN BMG/Piezas impresas/Cadenetas/Cadeneta 5/Soporte electronica.SLDPRT
108.0 x 33.0 x 37.0 mm
