campy/P3Steel-MGN-V19/P3Steel MGN BMG/Piezas impresas/Centrador Guia-Perfil3030.STL

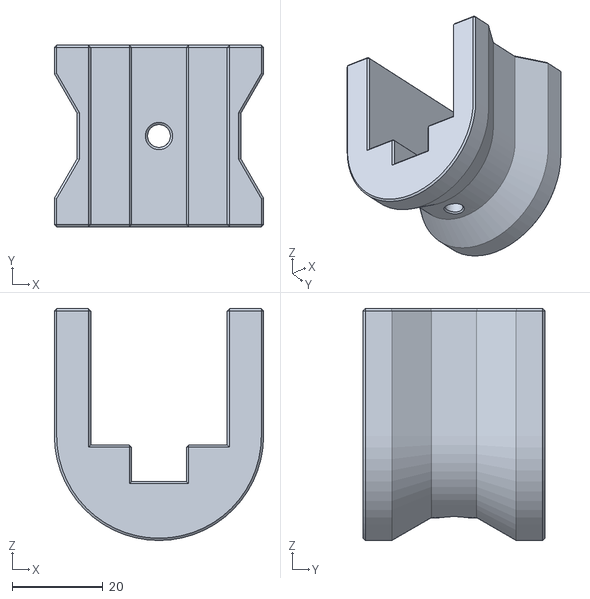
[picture p83: CAD file, 2019-10-11]
P3Steel MGN BMG/Piezas impresas/Centrador Guia-Perfil3030.STL
46.0 x 40.0 x 51.0
