campy/P3Steel-MGN-V19/P3Steel MGN BMG/Piezas impresas/F-Sensor/Sensor con endstop/Tapa F-Sensor.SLDPRT

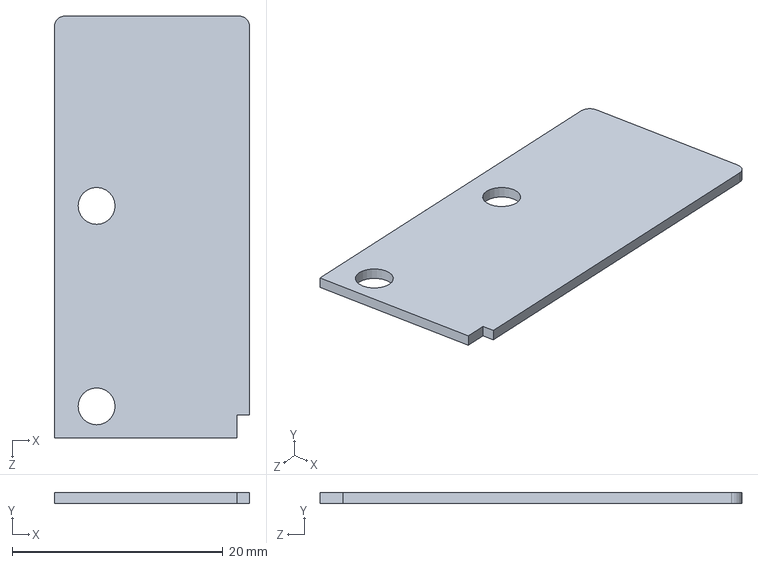
[picture p84: CAD file, 2019-06-21]
P3Steel MGN BMG/Piezas impresas/F-Sensor/Sensor con endstop/Tapa F-Sensor.SLDPRT
18.5 x 1.00 x 40.0 mm
