campy/P3Steel-MGN-V19/P3Steel MGN BMG/Piezas impresas/F-Sensor/Sensor filamento 2.0/Soporte sensor filamento.SLDPRT

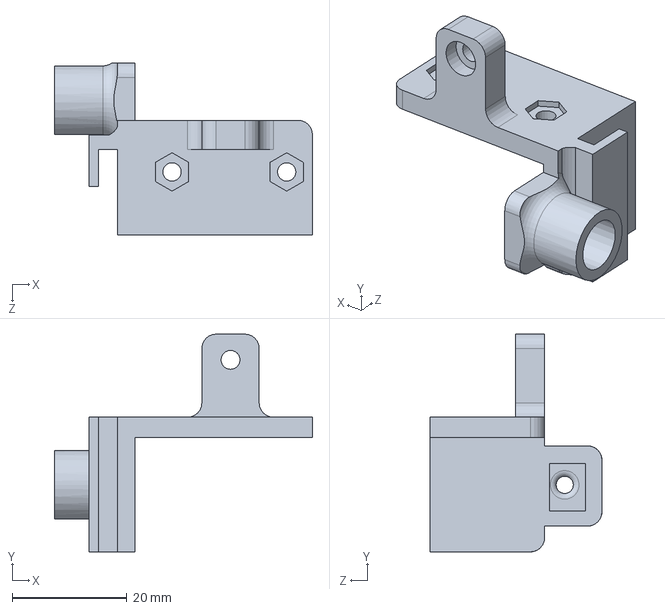
[picture p85: CAD file, 2019-06-27]
P3Steel MGN BMG/Piezas impresas/F-Sensor/Sensor filamento 2.0/Soporte sensor filamento.SLDPRT
45.0 x 38.0 x 30.0 mm
