campy/P3Steel-MGN-V19/P3Steel MGN BMG/Piezas impresas/LCD Cajas/Duet 7 Pulgadas/Delantera.SLDPRT

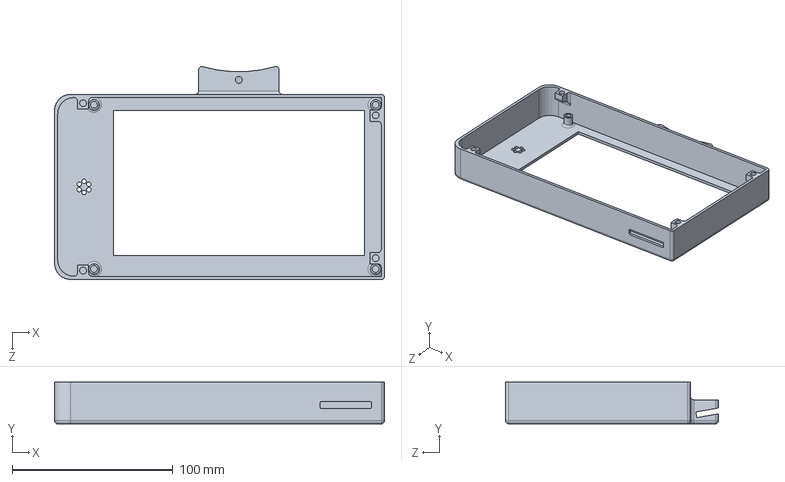
[picture p86: CAD file, 2019-06-27]
P3Steel MGN BMG/Piezas impresas/LCD Cajas/Duet 7 Pulgadas/Delantera.SLDPRT
205.0 x 26.0 x 132.3 mm
