campy/P3Steel-MGN-V19/P3Steel MGN BMG/Piezas impresas/LCD Cajas/Grapa LCD2.SLDPRT

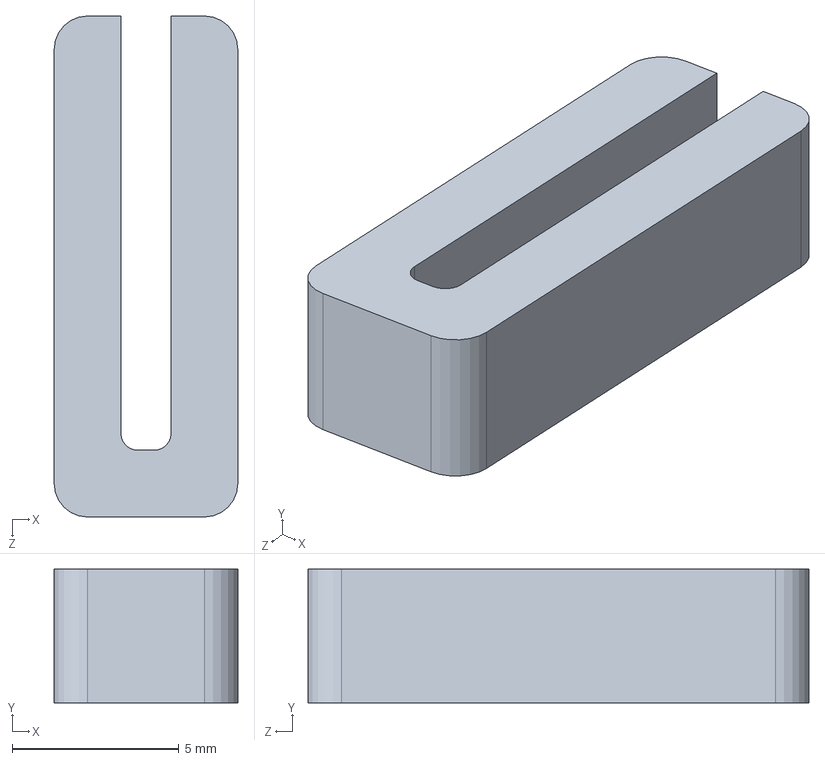
[picture p87: CAD file, 2019-06-21]
P3Steel MGN BMG/Piezas impresas/LCD Cajas/Grapa LCD2.SLDPRT
5.50 x 4.00 x 15.0 mm
