campy/P3Steel-MGN-V19/P3Steel MGN BMG/Piezas impresas/LCD Cajas/Mini 12864 RGB V1.2/Tapa.SLDPRT

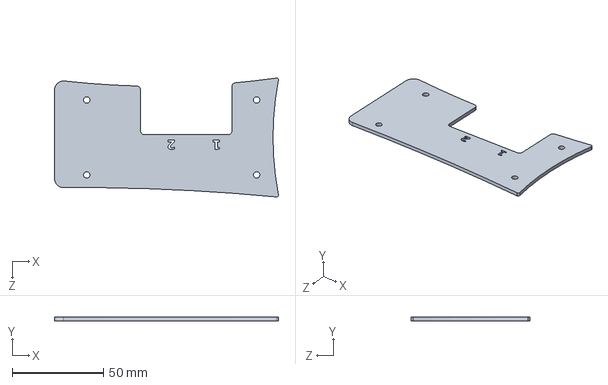
[picture p88: CAD file, 2019-09-13]
P3Steel MGN BMG/Piezas impresas/LCD Cajas/Mini 12864 RGB V1.2/Tapa.SLDPRT
122.6 x 2.00 x 65.1 mm
