campy/P3Steel-MGN-V19/P3Steel MGN BMG/Piezas impresas/LCD Cajas/MKS12864 Soporte Marco/LCD Tapa support.STL

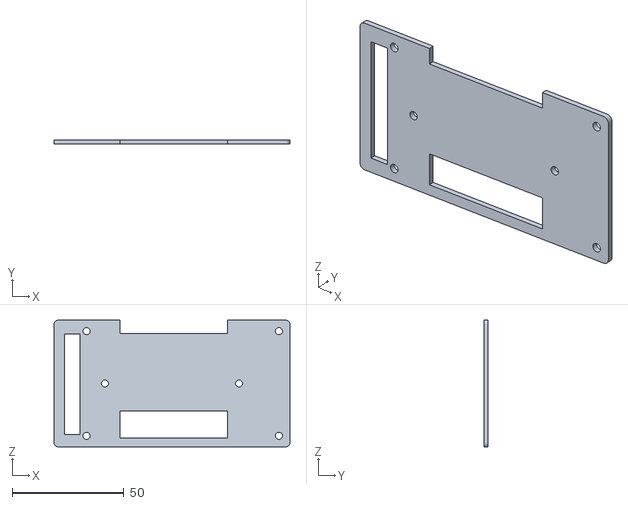
[picture p89: CAD file, 2019-06-21]
P3Steel MGN BMG/Piezas impresas/LCD Cajas/MKS12864 Soporte Marco/LCD Tapa support.STL
105.5 x 2.00 x 56.7
