campy/P3Steel-MGN-V19/P3Steel MGN BMG/Piezas impresas/LCD Cajas/MKS12864/LCD Case L Rear.STL

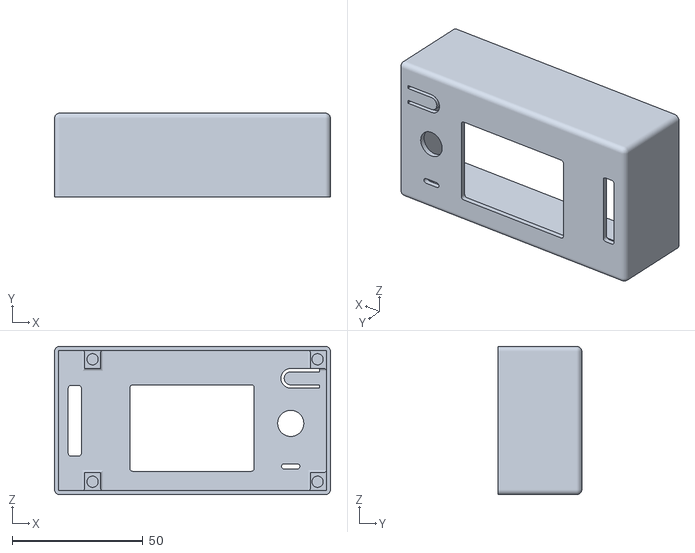
[picture p90: CAD file, 2019-06-21]
P3Steel MGN BMG/Piezas impresas/LCD Cajas/MKS12864/LCD Case L Rear.STL
105.5 x 32.0 x 56.7
