campy/P3Steel-MGN-V19/P3Steel MGN BMG/Piezas impresas/Protectores ventiladores/60mm_crosshair_reduced_fan_cover.stl

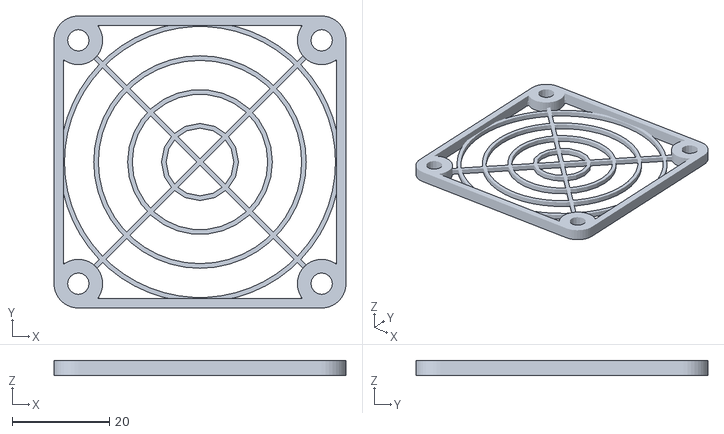
[picture p91: CAD file, 2019-06-21]
P3Steel MGN BMG/Piezas impresas/Protectores ventiladores/60mm_crosshair_reduced_fan_cover.stl
60.0 x 60.0 x 3.00
