campy/P3Steel-MGN-V19/P3Steel MGN BMG/Piezas impresas/Soportes electronicas/Caja MKS SKR/CajaMKSGen.SLDPRT

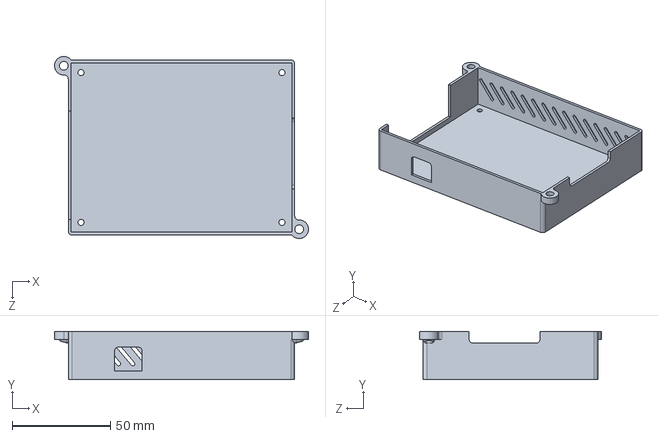
[picture p92: CAD file, 2019-06-21]
P3Steel MGN BMG/Piezas impresas/Soportes electronicas/Caja MKS SKR/CajaMKSGen.SLDPRT
129.0 x 24.5 x 92.4 mm
