campy/P3Steel-MGN-V19/P3Steel MGN BMG/Piezas impresas/Soportes electronicas/Placas/MKS Gen L/Makerbase GEN.SLDPRT

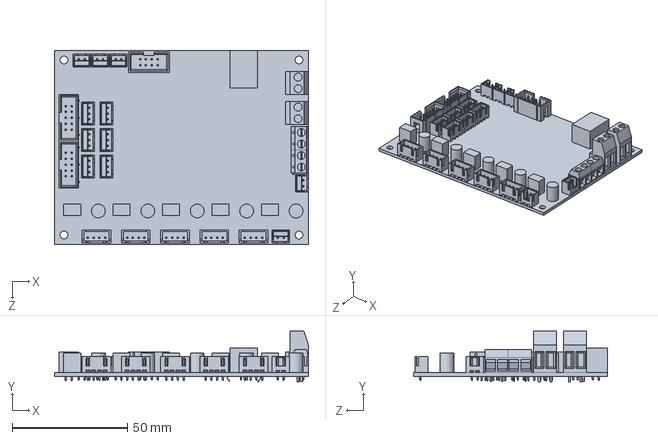
[picture p93: CAD file, 2019-09-13]
P3Steel MGN BMG/Piezas impresas/Soportes electronicas/Placas/MKS Gen L/Makerbase GEN.SLDPRT
110.0 x 22.1 x 84.0 mm
