campy/P3Steel-MGN-V19/P3Steel MGN BMG/Piezas impresas/Soportes electronicas/Placas/Raspi3B+_Mock.SLDPRT

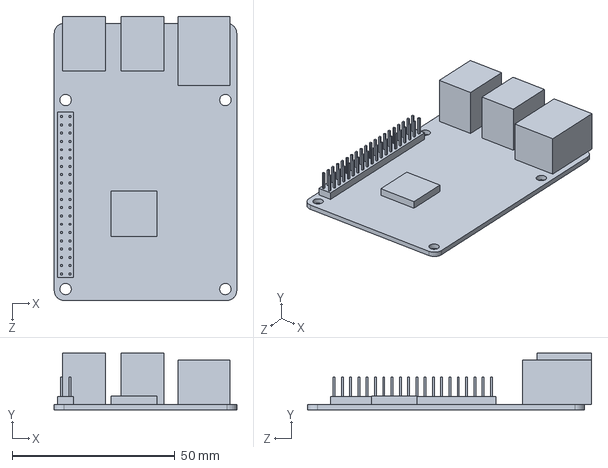
[picture p94: CAD file, 2019-09-13]
P3Steel MGN BMG/Piezas impresas/Soportes electronicas/Placas/Raspi3B+_Mock.SLDPRT
56.0 x 17.4 x 87.1 mm
