campy/P3Steel-MGN-V19/P3Steel MGN BMG/Piezas impresas/Soportes electronicas/Soporte Raspberry.SLDPRT

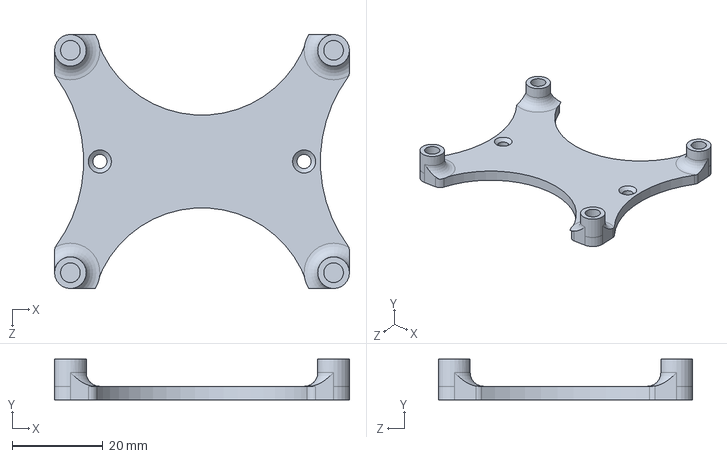
[picture p95: CAD file, 2019-09-13]
P3Steel MGN BMG/Piezas impresas/Soportes electronicas/Soporte Raspberry.SLDPRT
65.0 x 9.00 x 56.0 mm
