campy/P3Steel-MGN-V19/P3Steel MGN BMG/Piezas impresas/Soportes electronicas/Tapa Electronica/Tapa Electronica SKR-Raspy.SLDPRT

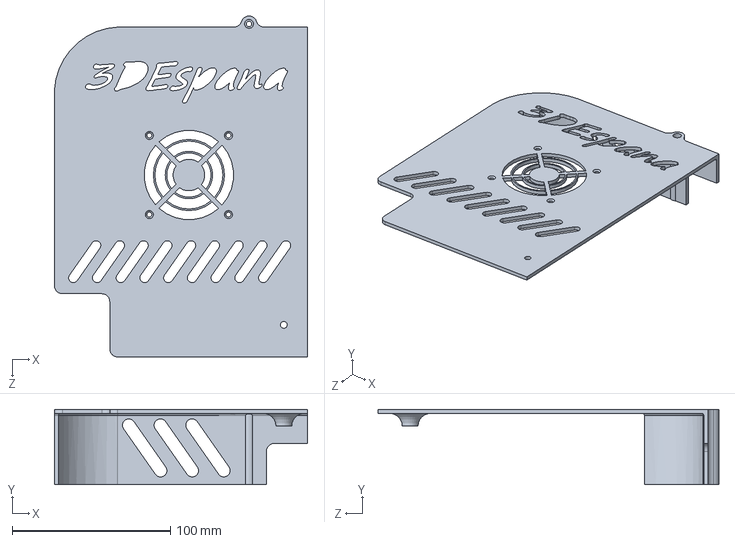
[picture p96: CAD file, 2019-09-13]
P3Steel MGN BMG/Piezas impresas/Soportes electronicas/Tapa Electronica/Tapa Electronica SKR-Raspy.SLDPRT
160.0 x 47.5 x 215.5 mm
