campy/P3Steel-MGN-V19/P3Steel MGN BMG/Piezas impresas/Tapas perfiles/Tapa delantera L.SLDPRT

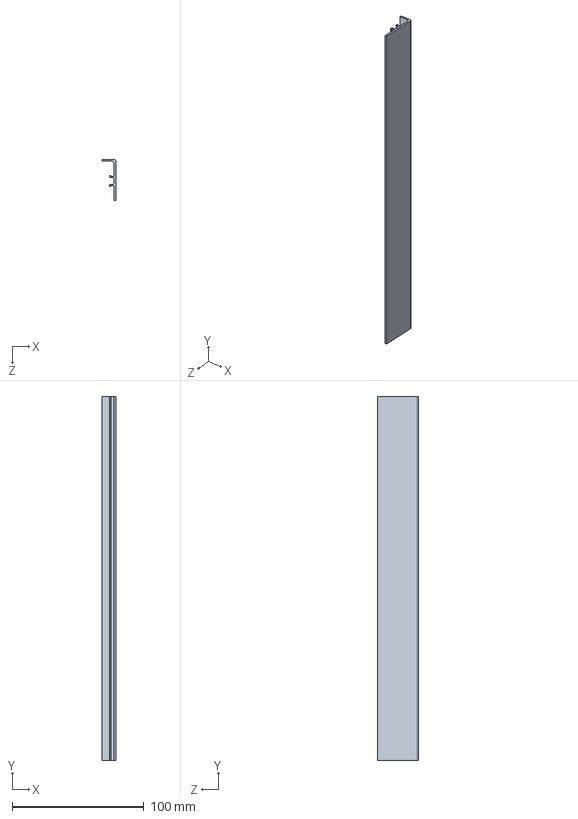
[picture p97: CAD file, 2019-09-13]
P3Steel MGN BMG/Piezas impresas/Tapas perfiles/Tapa delantera L.SLDPRT
10.4 x 276.5 x 31.5 mm
