campy/P3Steel-MGN-V19/P3Steel MGN BMG/Source/3mm Pulley/PULLEY 16T GT-2.SLDPRT

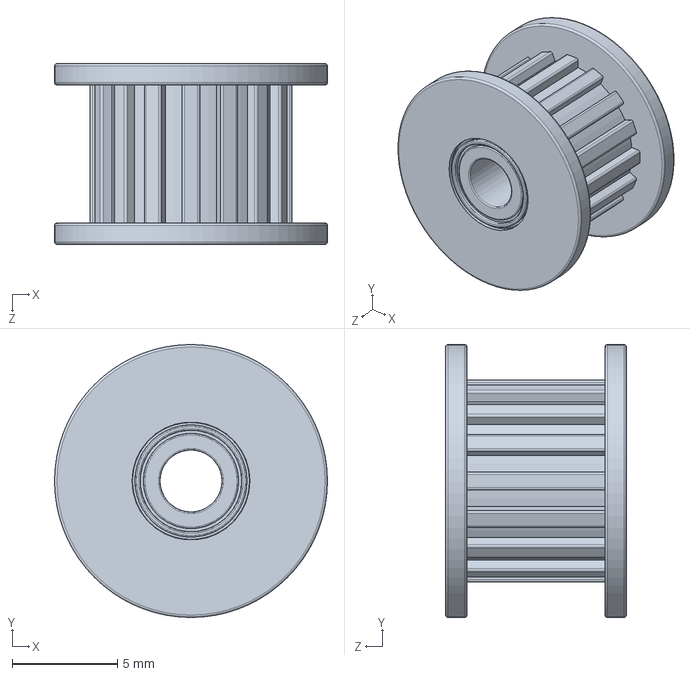
[picture p98: CAD file, 2019-06-21]
P3Steel MGN BMG/Source/3mm Pulley/PULLEY 16T GT-2.SLDPRT
13.0 x 13.0 x 8.59 mm
