campy/P3Steel-MGN-V19/P3Steel MGN BMG/Source/4x12.SLDPRT

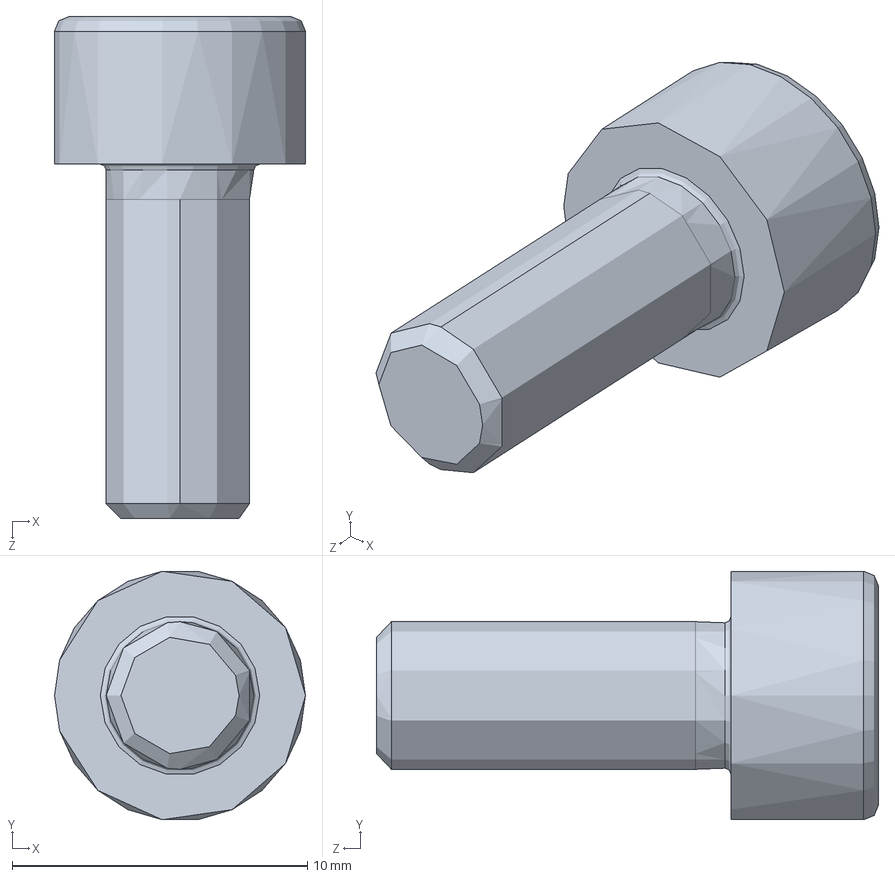
[picture p99: CAD file, 2019-09-13]
P3Steel MGN BMG/Source/4x12.SLDPRT
8.50 x 8.41 x 17.0 mm
