campy/P3Steel-MGN-V19/P3Steel MGN BMG/Source/BMG/BMG_Extruder v3.sldprt

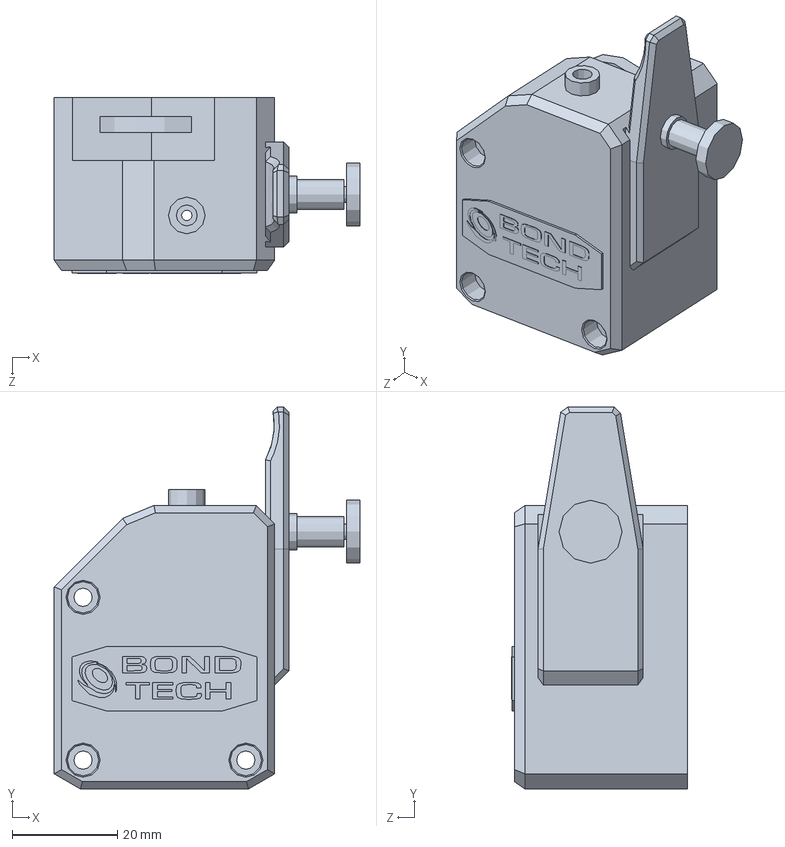
[picture p100: CAD file, 2019-09-13]
P3Steel MGN BMG/Source/BMG/BMG_Extruder v3.sldprt
58.2 x 72.8 x 33.6 mm
