campy/P3Steel-MGN-V19/P3Steel MGN BMG/Source/Conector C14/rocker.SLDPRT

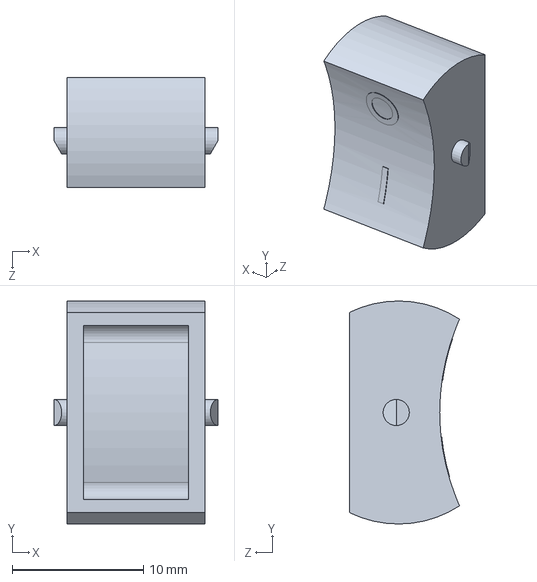
[picture p101: CAD file, 2019-09-13]
P3Steel MGN BMG/Source/Conector C14/rocker.SLDPRT
12.5 x 17.0 x 8.39 mm
