campy/P3Steel-MGN-V19/P3Steel MGN BMG/Source/F688zz/F688ZZ_Housing.SLDPRT

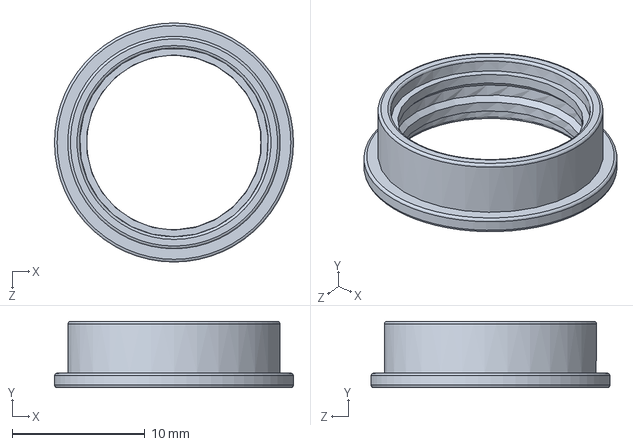
[picture p102: CAD file, 2019-06-21]
P3Steel MGN BMG/Source/F688zz/F688ZZ_Housing.SLDPRT
18.0 x 5.00 x 18.0 mm
