campy/P3Steel-MGN-V19/P3Steel MGN BMG/Source/Inductive Sensor/Гайка М12.SLDPRT

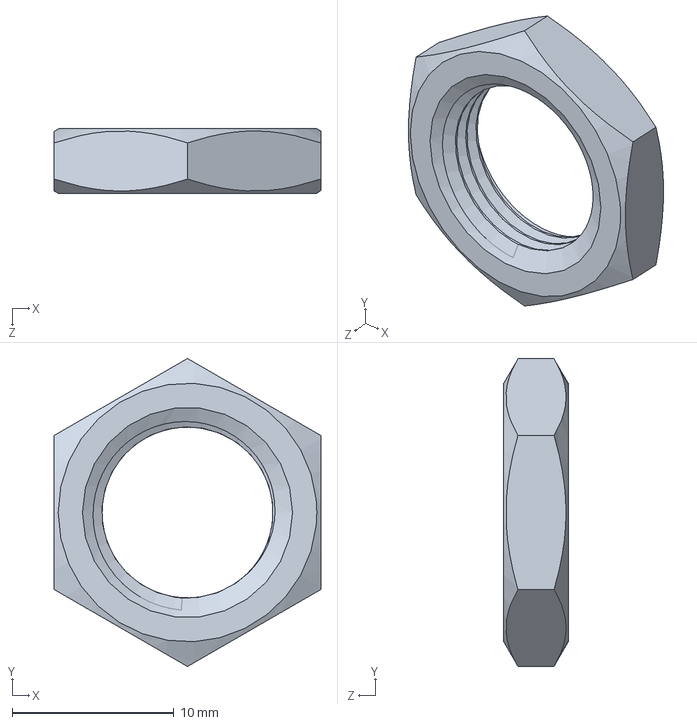
[picture p103: CAD file, 2019-09-13]
P3Steel MGN BMG/Source/Inductive Sensor/Гайка М12.SLDPRT
16.5 x 19.1 x 4.00 mm
