campy/P3Steel-MGN-V19/P3Steel MGN BMG/Source/LCD/MKS mini LCD.IGS

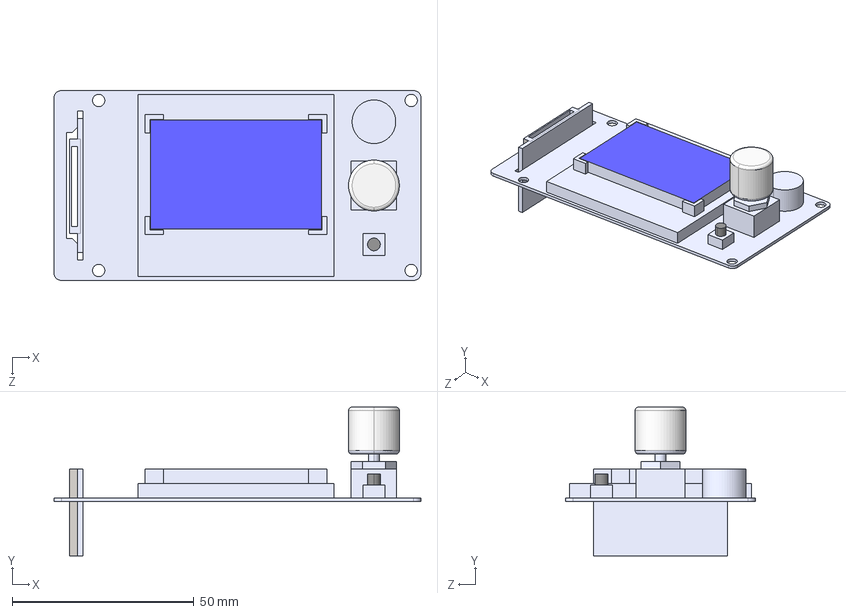
[picture p104: CAD file, 2019-06-21]
P3Steel MGN BMG/Source/LCD/MKS mini LCD.IGS
101.0 x 41.0 x 52.2 mm
