campy/P3Steel-MGN-V19/P3Steel MGN BMG/Source/MGN12C300/MGN12C300.SLDPRT

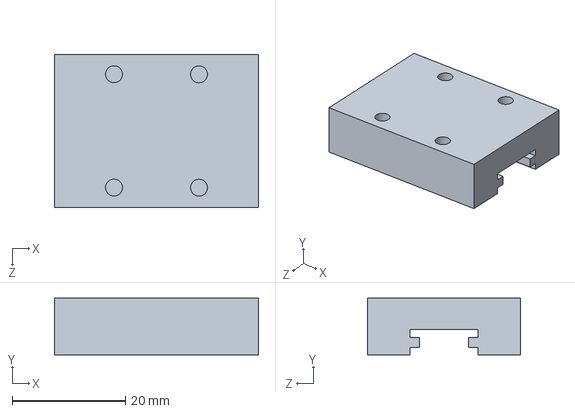
[picture p105: CAD file, 2019-09-13]
P3Steel MGN BMG/Source/MGN12C300/MGN12C300.SLDPRT
36.0 x 10.0 x 27.0 mm
