campy/P3Steel-MGN-V19/P3Steel MGN BMG/Source/MGN12C400/MGN12C.SLDPRT

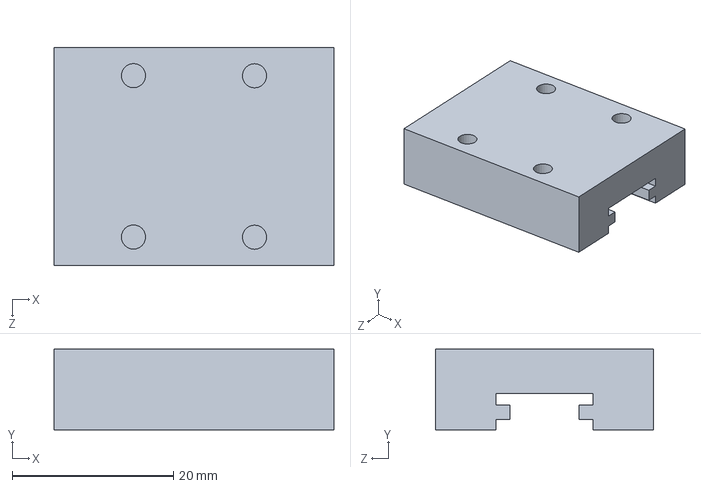
[picture p106: CAD file, 2019-09-13]
P3Steel MGN BMG/Source/MGN12C400/MGN12C.SLDPRT
34.7 x 10.0 x 27.0 mm
