campy/P3Steel-MGN-V19/P3Steel MGN BMG/Source/Mot Y/nema_17_motor.SLDPRT

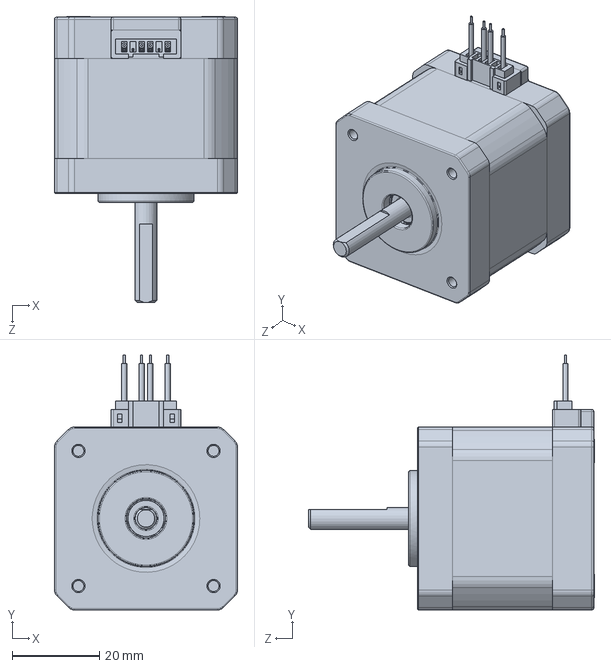
[picture p107: CAD file, 2019-09-13]
P3Steel MGN BMG/Source/Mot Y/nema_17_motor.SLDPRT
42.0 x 58.5 x 65.7 mm
