campy/P3Steel-MGN-V19/P3Steel MGN BMG/Source/Nema Y/Stepper motor/Part1.SLDPRT

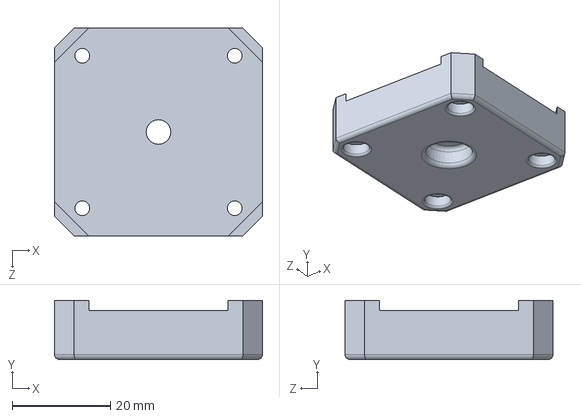
[picture p108: CAD file, 2019-09-13]
P3Steel MGN BMG/Source/Nema Y/Stepper motor/Part1.SLDPRT
42.3 x 12.0 x 42.3 mm
