campy/P3Steel-MGN-V19/P3Steel MGN BMG/Source/Power Supply/MW_switching_25A.SLDPRT

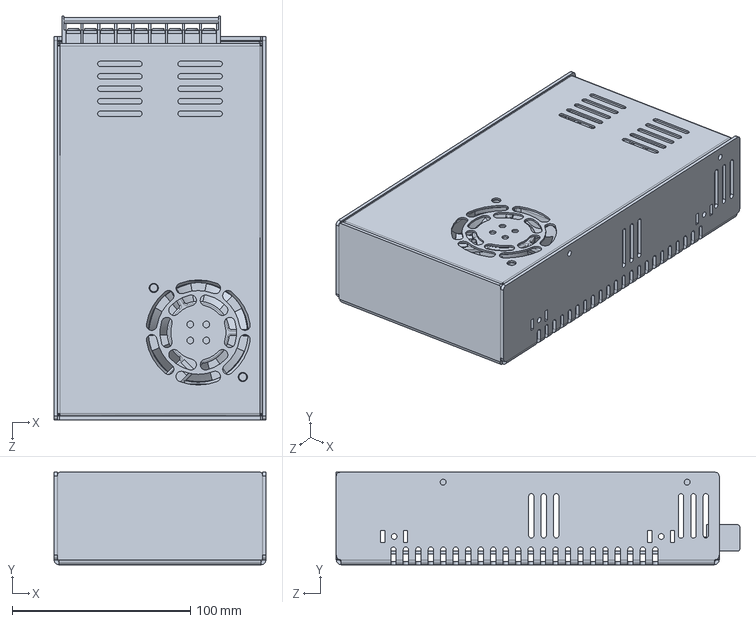
[picture p109: CAD file, 2019-09-13]
P3Steel MGN BMG/Source/Power Supply/MW_switching_25A.SLDPRT
119.0 x 52.0 x 226.5 mm
