campy/P3Steel-MGN-V19/P3Steel MGN BMG/Source/Radial Cooling Fan 50mm DC12V/top.SLDPRT

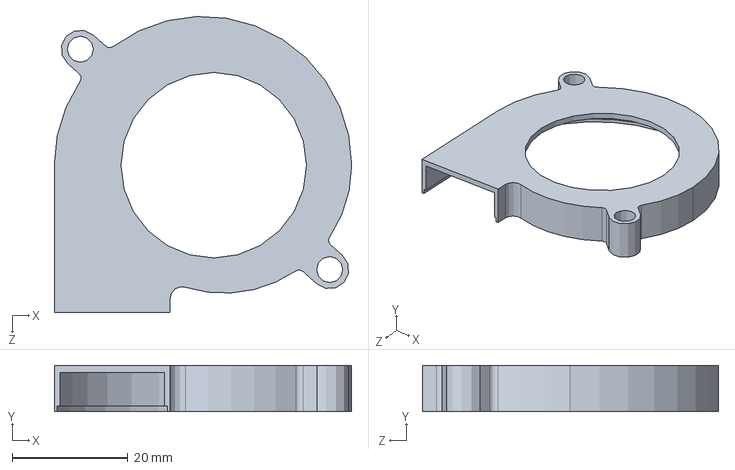
[picture p110: CAD file, 2019-09-13]
P3Steel MGN BMG/Source/Radial Cooling Fan 50mm DC12V/top.SLDPRT
51.3 x 8.00 x 51.0 mm
