campy/P3Steel-MGN-V19/P3Steel MGN BMG/Source/Titan Aero/Titan Aero P3steel/Blower titan/Titan_Aero_Shroud_Front.stl

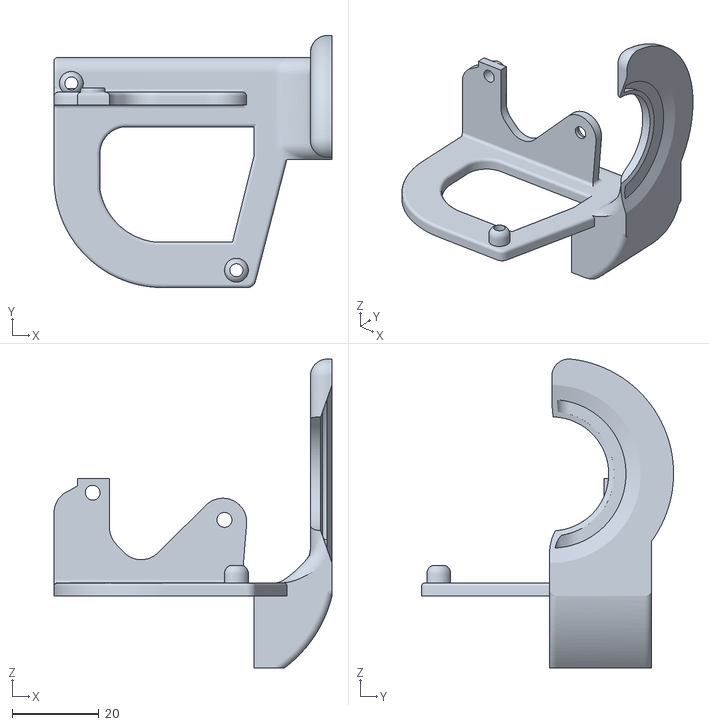
[picture p111: CAD file, 2019-06-21]
P3Steel MGN BMG/Source/Titan Aero/Titan Aero P3steel/Blower titan/Titan_Aero_Shroud_Front.stl
64.0 x 58.0 x 71.1
