campy/P3Steel-MGN-V19/P3Steel MGN BMG/Source/Titan Aero/Titan Aero P3steel/Nema 17 Corto/Nema 17.SLDPRT

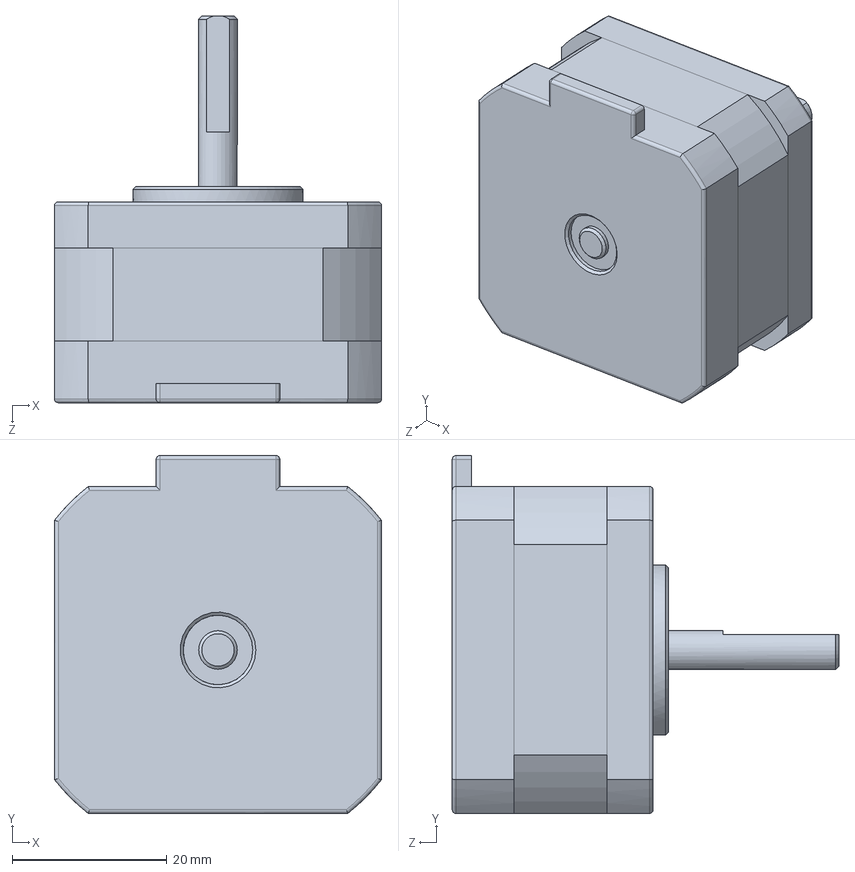
[picture p112: CAD file, 2019-09-13]
P3Steel MGN BMG/Source/Titan Aero/Titan Aero P3steel/Nema 17 Corto/Nema 17.SLDPRT
42.3 x 46.3 x 50.0 mm
