campy/P3Steel-MGN-V19/P3Steel MGN BMG/Source/Titan Aero/Titan Aero P3steel/Radial Cooling Fan 50mm DC12V/Radial-Cooling-Fan-5015-DC12V.STEP

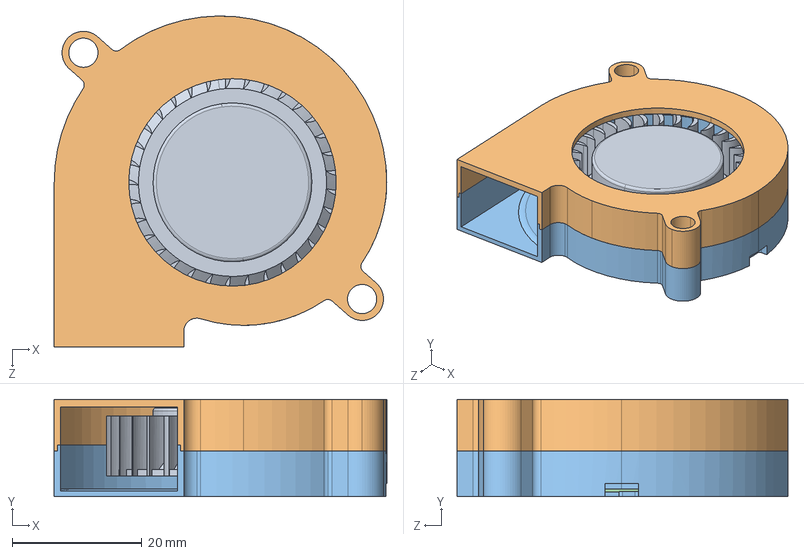
[picture p113: CAD file, 2019-06-21]
P3Steel MGN BMG/Source/Titan Aero/Titan Aero P3steel/Radial Cooling Fan 50mm DC12V/Radial-Cooling-Fan-5015-DC12V.STEP
51.3 x 15.0 x 51.1 mm
turbine
top
bottom
