campy/P3Steel-MGN-V19/P3Steel MGN BMG/Source/Tuerca Anti-Back/sprezyna nakretka tr 8.stp

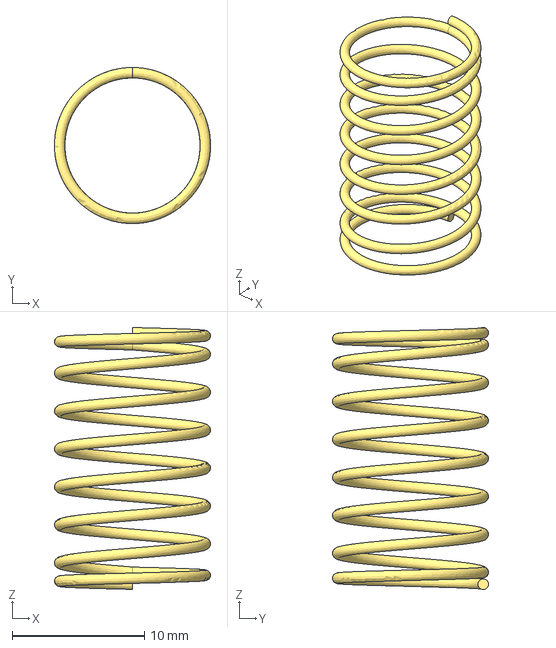
[picture p114: CAD file, 2019-06-21]
P3Steel MGN BMG/Source/Tuerca Anti-Back/sprezyna nakretka tr 8.stp
11.8 x 11.8 x 19.8 mm
