campy/P3Steel-MGN-V19/P3Steel MGN Titan/Bandeja 300V2.SLDPRT

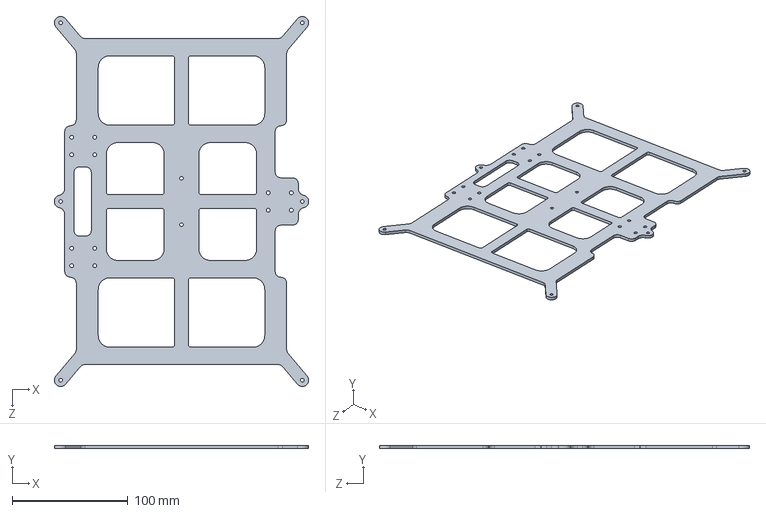
[picture p115: CAD file, 2020-01-10]
P3Steel MGN Titan/Bandeja 300V2.SLDPRT
220.0 x 3.00 x 320.0 mm
