campy/P3Steel-MGN-V19/P3Steel MGN Titan/DXF/Iman Bandeja/Iman Bandeja.SLDPRT

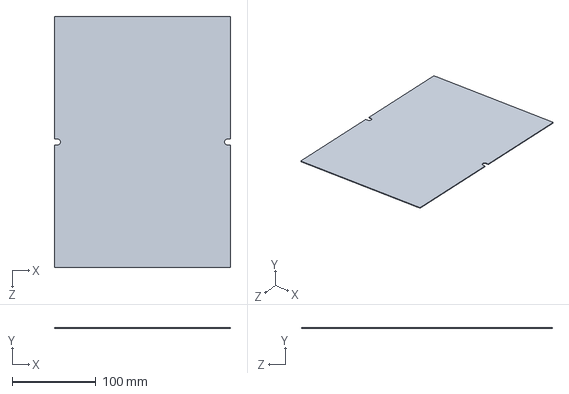
[picture p116: CAD file, 2019-06-21]
P3Steel MGN Titan/DXF/Iman Bandeja/Iman Bandeja.SLDPRT
210.0 x 1.00 x 300.0 mm
