campy/P3Steel-MGN-V19/P3Steel MGN Titan/Extrusor/X-CarriageV2 Titan.SLDPRT

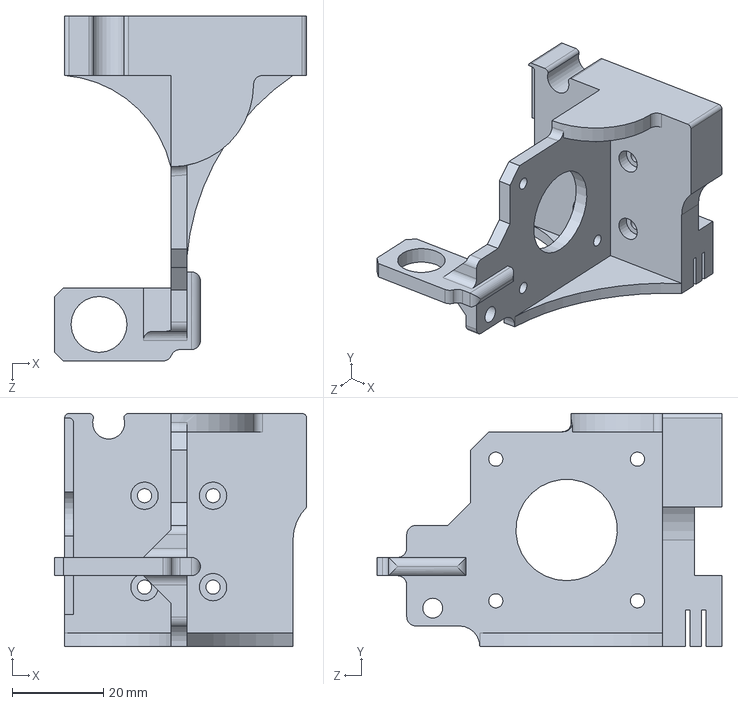
[picture p117: CAD file, 2019-09-07]
P3Steel MGN Titan/Extrusor/X-CarriageV2 Titan.SLDPRT
55.2 x 51.0 x 75.5 mm
