campy/P3Steel-MGN-V19/P3Steel MGN Titan/Piezas impresas/Cadenetas/Cadeneta 15/Eslabon 15.SLDPRT

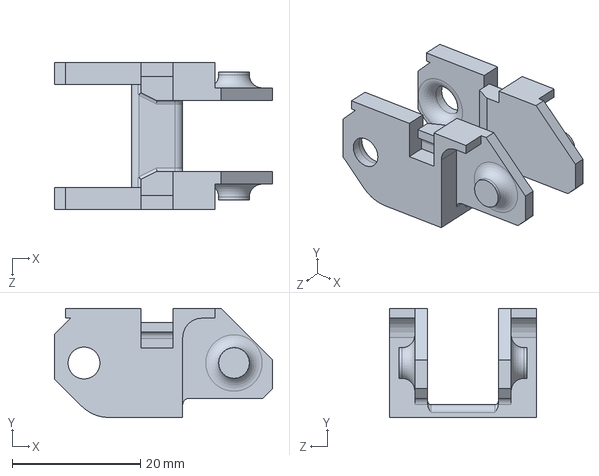
[picture p118: CAD file, 2019-09-07]
P3Steel MGN Titan/Piezas impresas/Cadenetas/Cadeneta 15/Eslabon 15.SLDPRT
34.0 x 17.0 x 23.0 mm
