campy/P3Steel-MGN-V19/P3Steel MGN Titan/Piezas impresas/Cadenetas/Cadeneta 5/Otros Tipos Eslabones/Soporte cama.SLDPRT

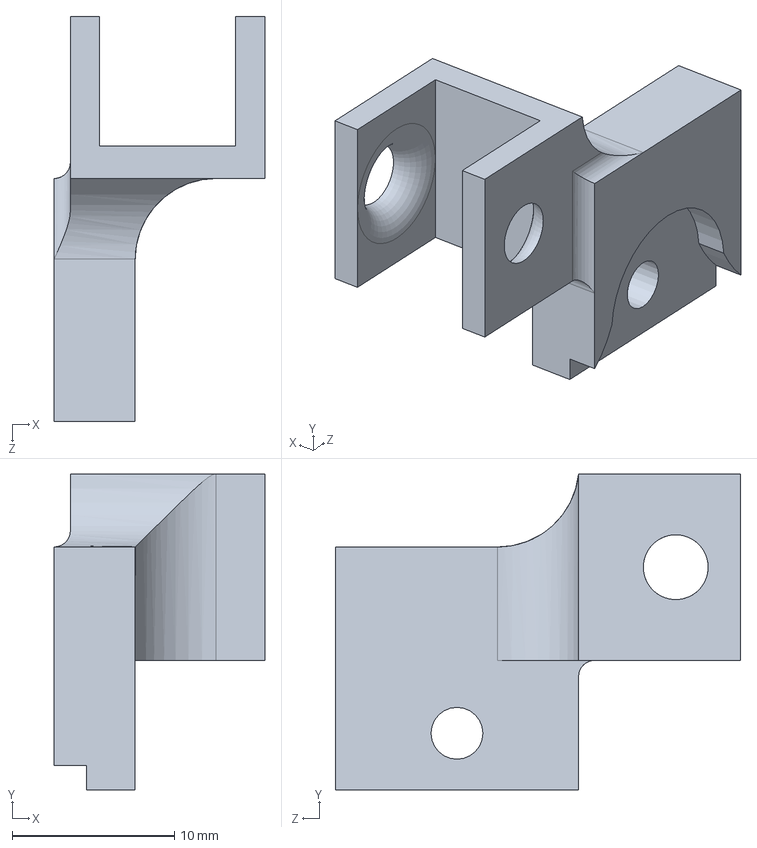
[picture p119: CAD file, 2019-06-21]
P3Steel MGN Titan/Piezas impresas/Cadenetas/Cadeneta 5/Otros Tipos Eslabones/Soporte cama.SLDPRT
13.0 x 19.5 x 25.0 mm
