campy/P3Steel-MGN-V19/P3Steel MGN Titan/Piezas impresas/Cadenetas/Cadeneta 5/Soporte bandeja V2.SLDPRT

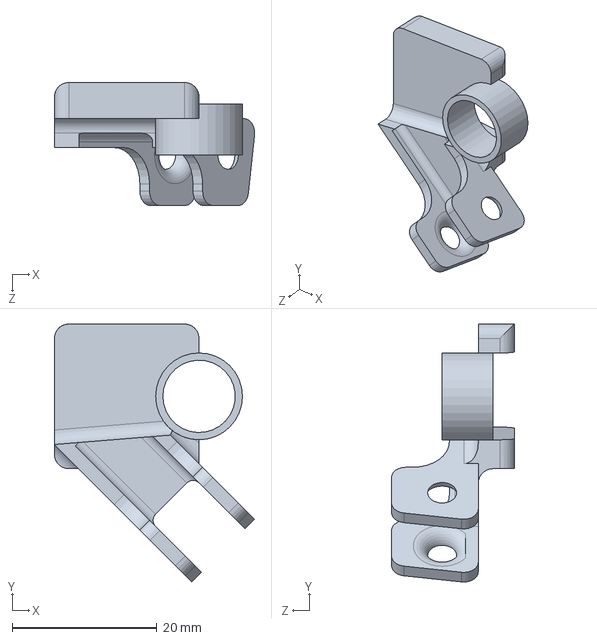
[picture p120: CAD file, 2019-10-11]
P3Steel MGN Titan/Piezas impresas/Cadenetas/Cadeneta 5/Soporte bandeja V2.SLDPRT
27.7 x 35.7 x 17.0 mm
