campy/P3Steel-MGN-V19/P3Steel MGN BMG/Source/F688zz/Renderings/F688ZZ_assembly.JPG

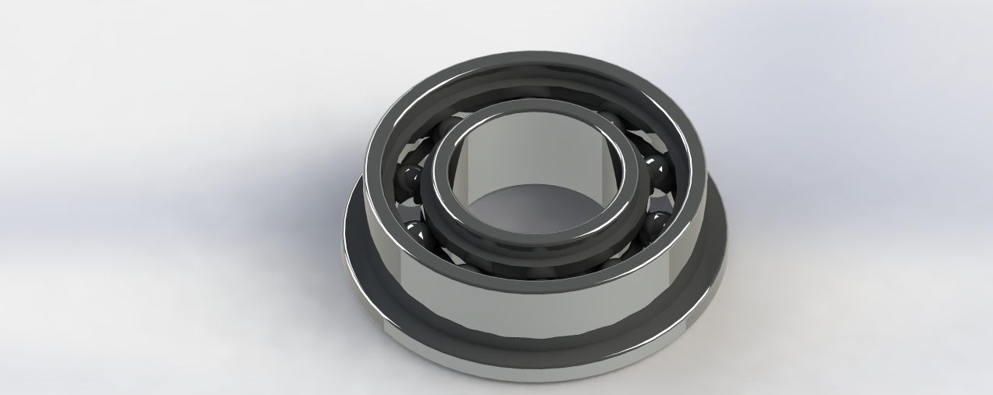
P3Steel MGN BMG/Source/F688zz/Renderings/F688ZZ_assembly.JPG
