campy/P3Steel-MGN-V19/P3Steel MGN Titan/Fotos ensamble/20191008_003216.jpg

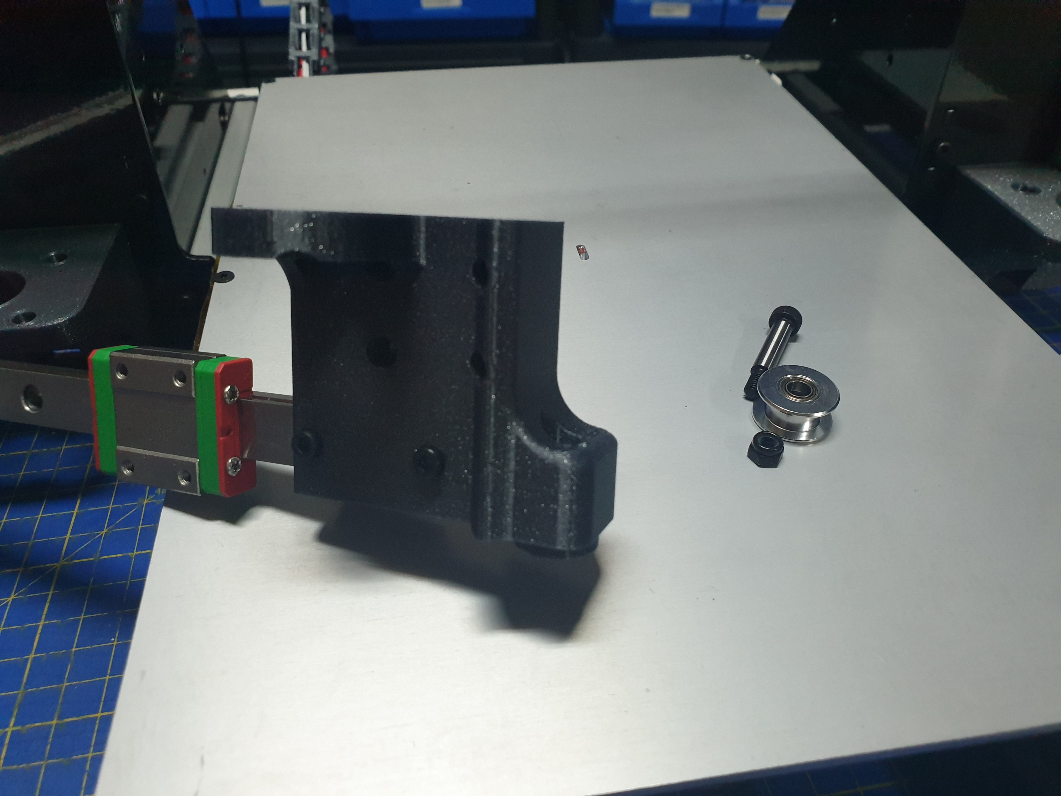
P3Steel MGN Titan/Fotos ensamble/20191008_003216.jpg
