campy/P3Steel-MGN-V19/P3Steel MGN Titan/Fotos ensamble/20191008_004411.jpg

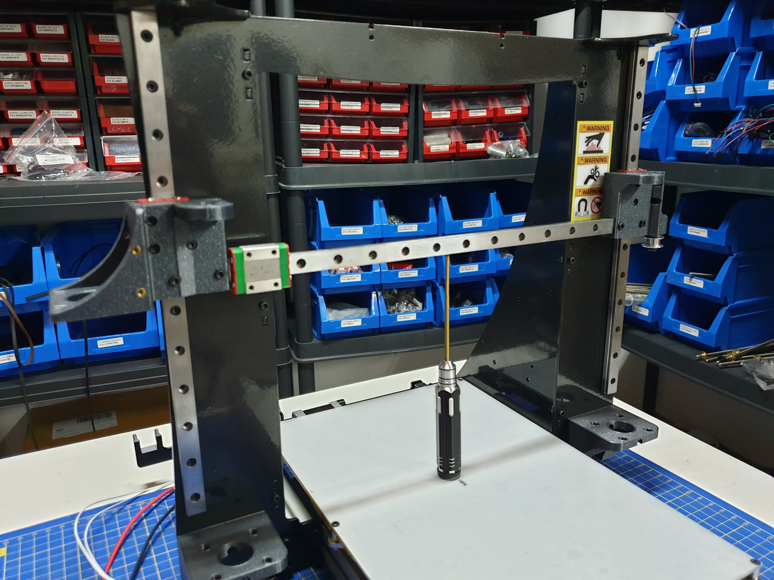
P3Steel MGN Titan/Fotos ensamble/20191008_004411.jpg
