campy/P3Steel-MGN-V19/P3Steel MGN Titan/Fotos ensamble/20191008_155220.jpg

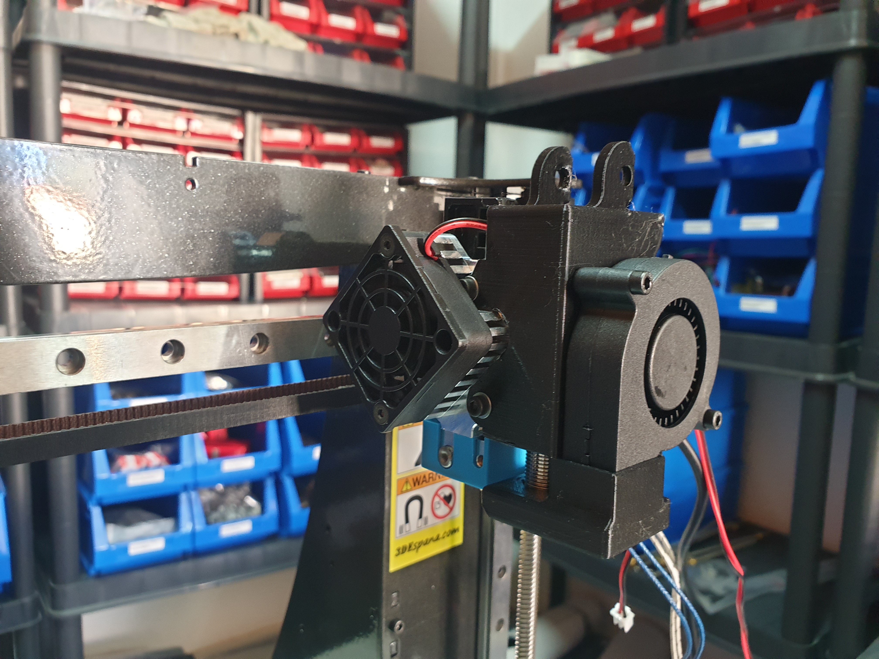
P3Steel MGN Titan/Fotos ensamble/20191008_155220.jpg
