campy/P3Steel-MGN-V19/P3Steel MGN Titan/Fotos ensamble/20191008_155746.jpg

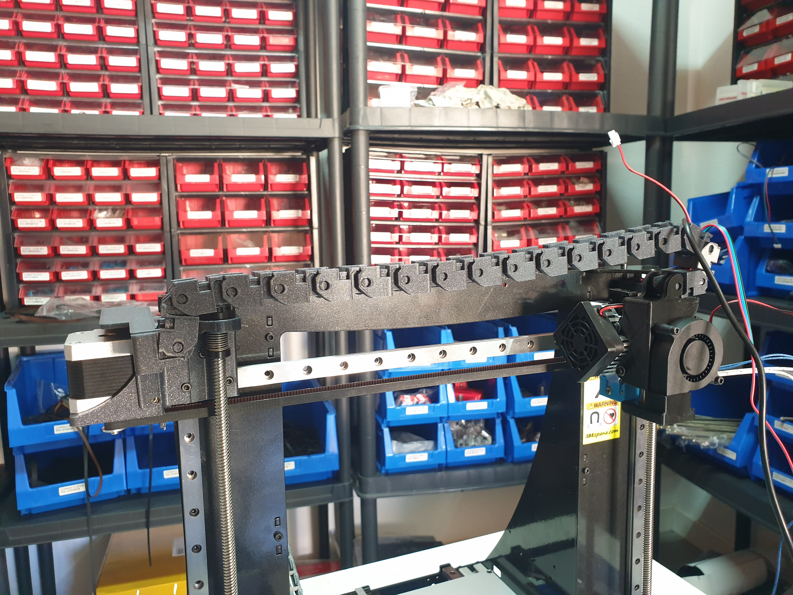
P3Steel MGN Titan/Fotos ensamble/20191008_155746.jpg
