campy/P3Steel-MGN-V19/P3Steel MGN Titan/Fotos ensamble/20191009_134107.jpg

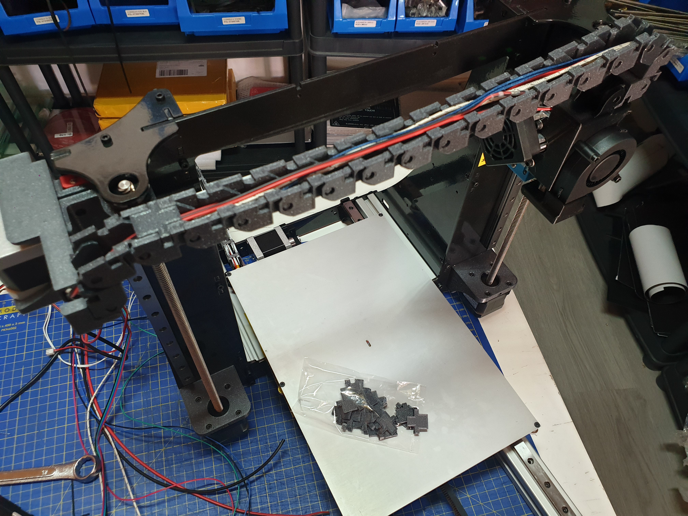
P3Steel MGN Titan/Fotos ensamble/20191009_134107.jpg
