campy/P3Steel-MGN-V19/P3Steel MGN Titan/Fotos ensamble/20191009_141108.jpg

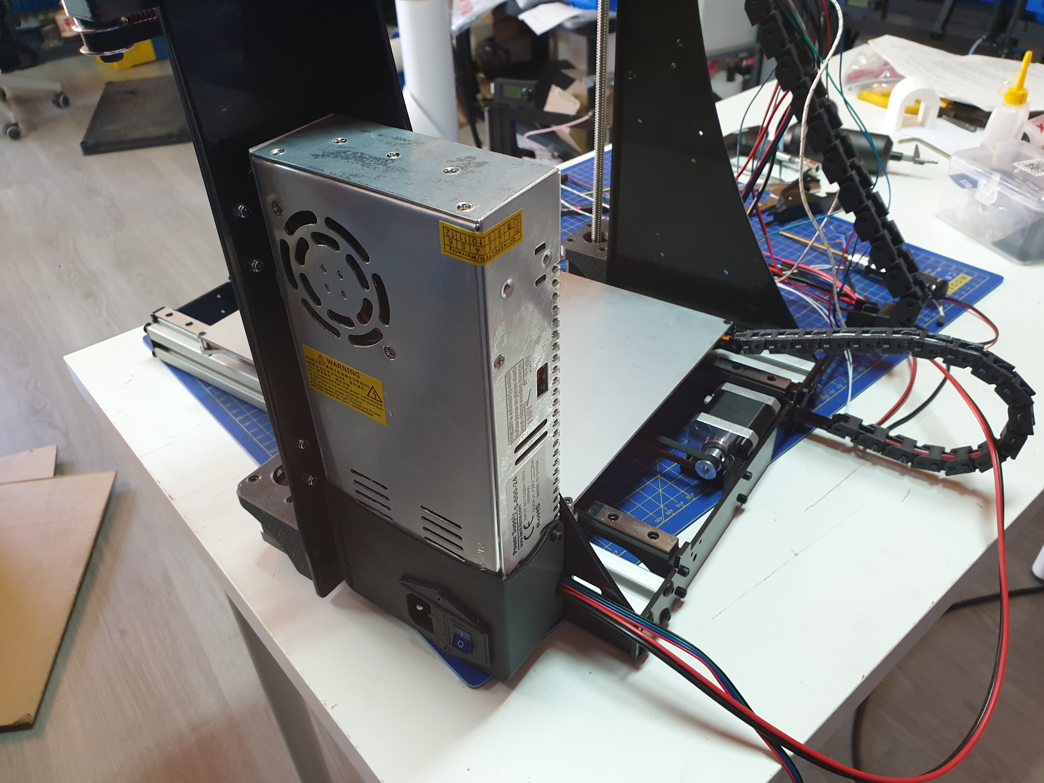
P3Steel MGN Titan/Fotos ensamble/20191009_141108.jpg
