campy/P3Steel-MGN-V19/P3Steel MGN BMG/Piezas impresas/Soportes electronicas/Placas/Duet Wifi/Duet Measures.png

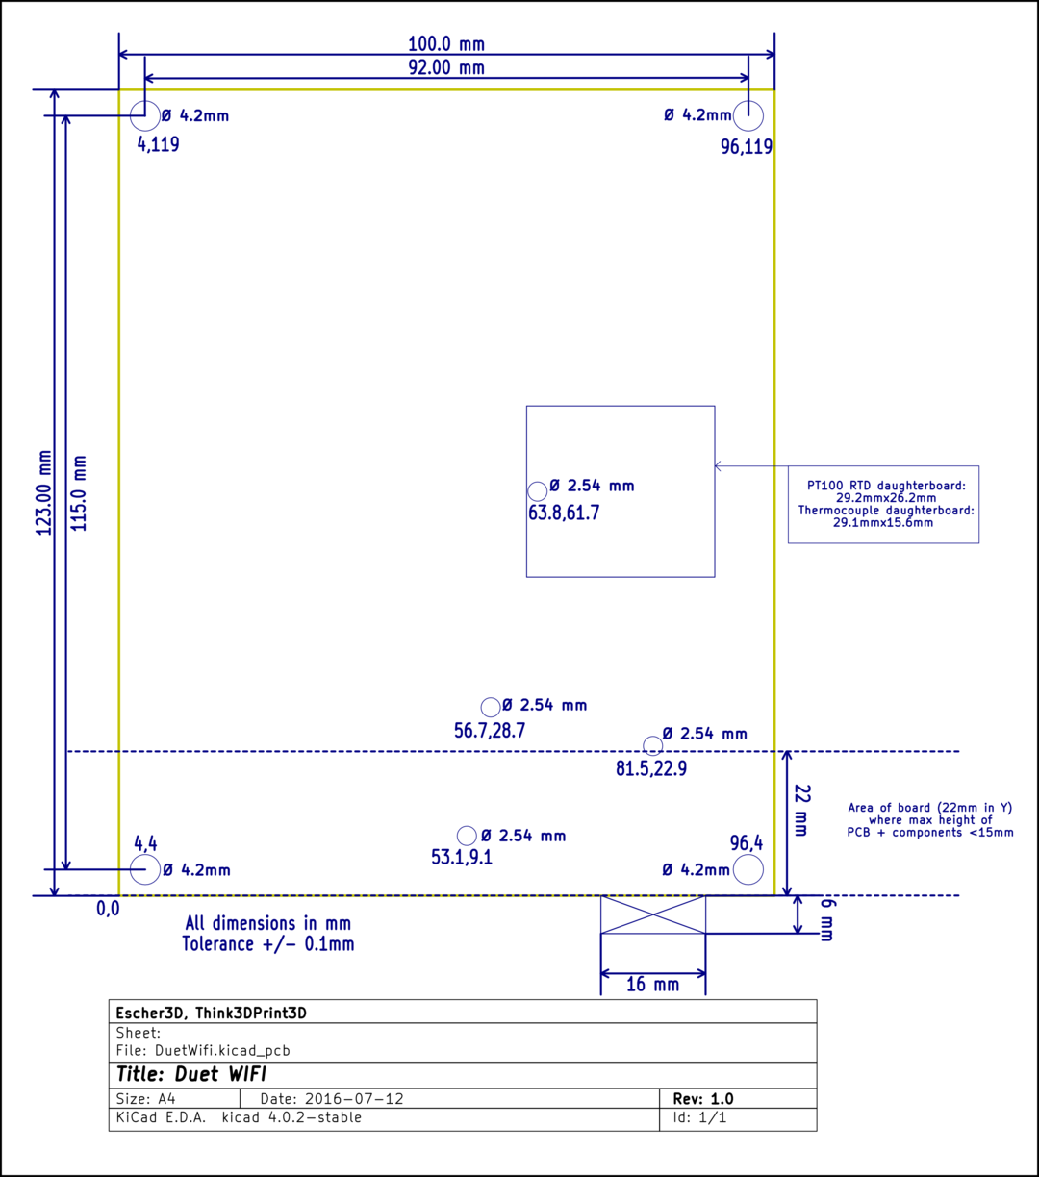
P3Steel MGN BMG/Piezas impresas/Soportes electronicas/Placas/Duet Wifi/Duet Measures.png
