campy/P3Steel-MGN-V19/P3Steel MGN Titan/Fotos ensamble/20191007_134448.jpg

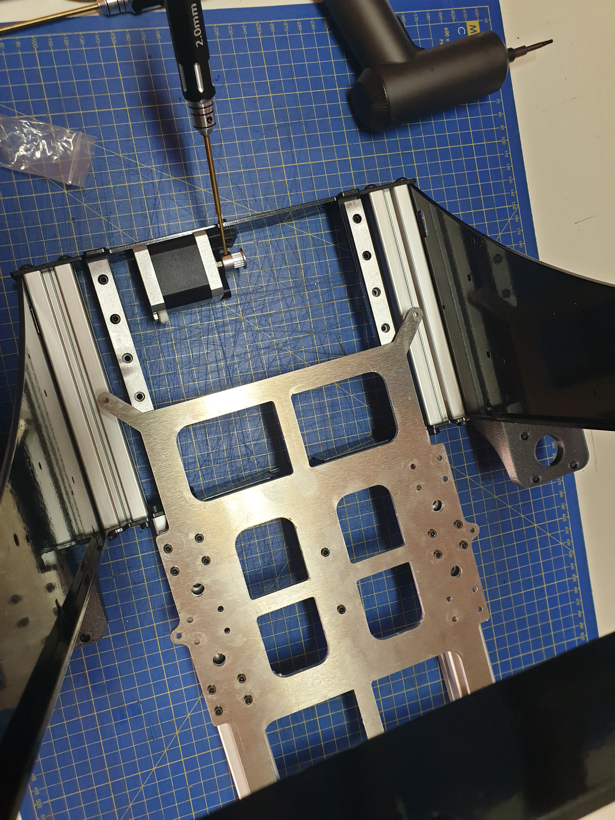
P3Steel MGN Titan/Fotos ensamble/20191007_134448.jpg
